hthant/snowteam_2023_2024/CFD/DPM/DPM 5/DPM Attempt 5_files/dp0/FFF-1/Fluent/animation-1_0196.png

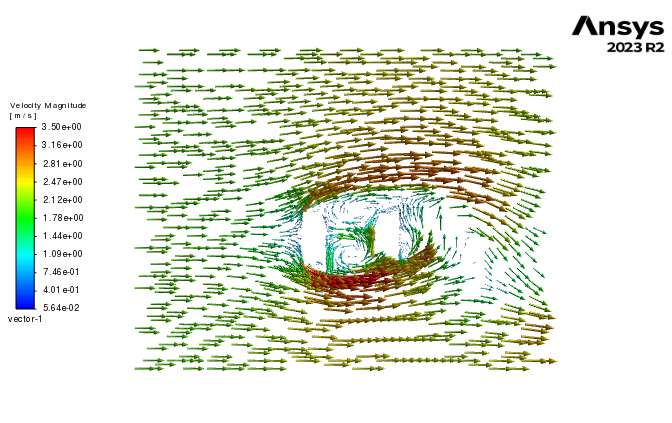
CFD/DPM/DPM 5/DPM Attempt 5_files/dp0/FFF-1/Fluent/animation-1_0196.png
