hthant/snowteam_2023_2024/CFD/Different Diameters/7_5_inch_diameter_files/progress_files/dp0/FFF-1/Fluent/vector-1.png

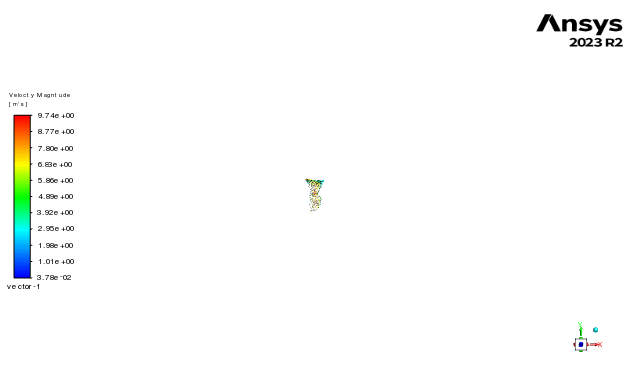
CFD/Different Diameters/7_5_inch_diameter_files/progress_files/dp0/FFF-1/Fluent/vector-1.png
