hthant/snowteam_2023_2024/CFD/DPM/DPM 5/Capture4.PNG

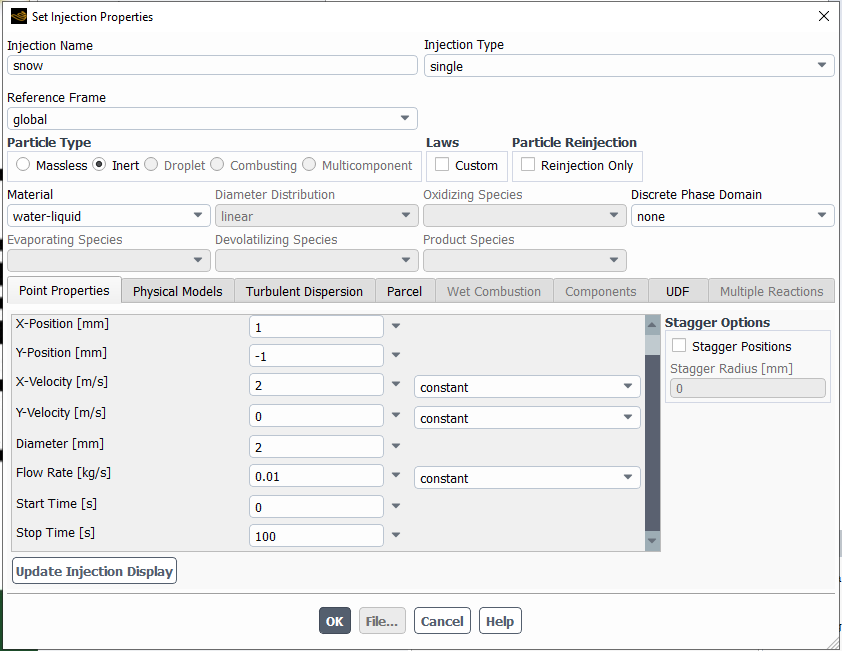
CFD/DPM/DPM 5/Capture4.PNG
