hthant/snowteam_2023_2024/CFD/DPM/DPM_Attempt1_files/progress_files/dp0/FFF/Fluent/particle-tracks-1.png

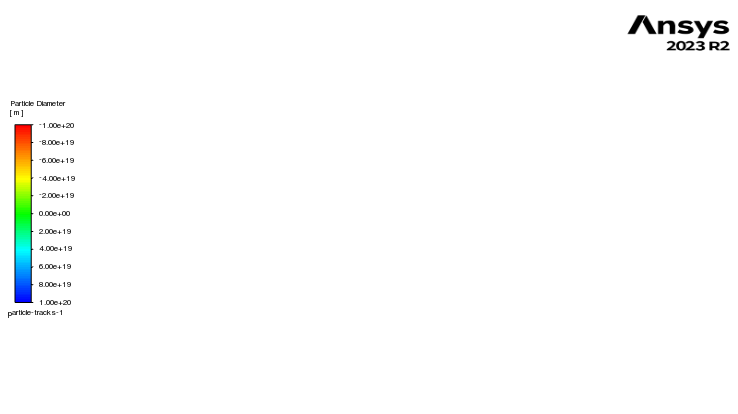
CFD/DPM/DPM_Attempt1_files/progress_files/dp0/FFF/Fluent/particle-tracks-1.png
