hthant/snowteam_2023_2024/Light Fixtures/Heatsink/Heatsink model with holes.png

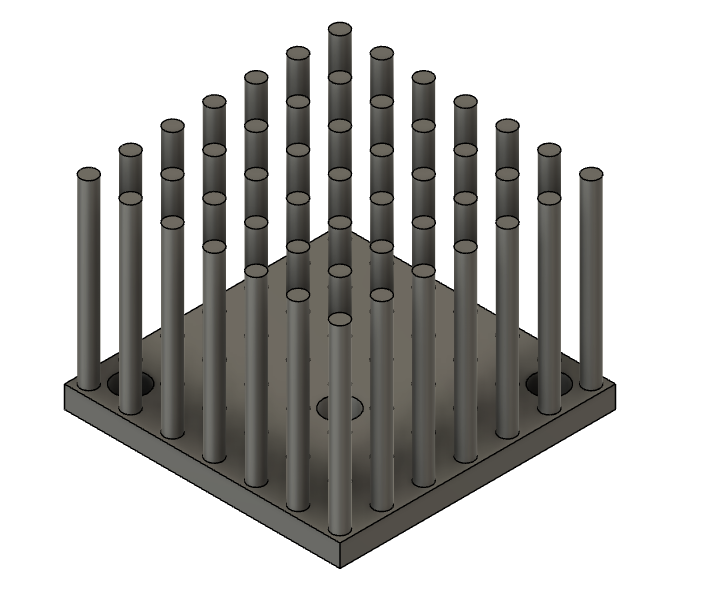
Light Fixtures/Heatsink/Heatsink model with holes.png
