hthant/snowteam_2023_2024/Light Fixtures/Heatsink/HoleDiagram.png

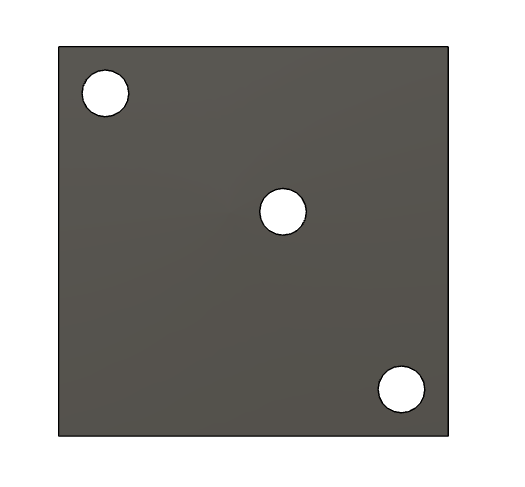
Light Fixtures/Heatsink/HoleDiagram.png
