hthant/snowteam_2023_2024/Light Fixtures/Heatsink/HoleDimensions.png

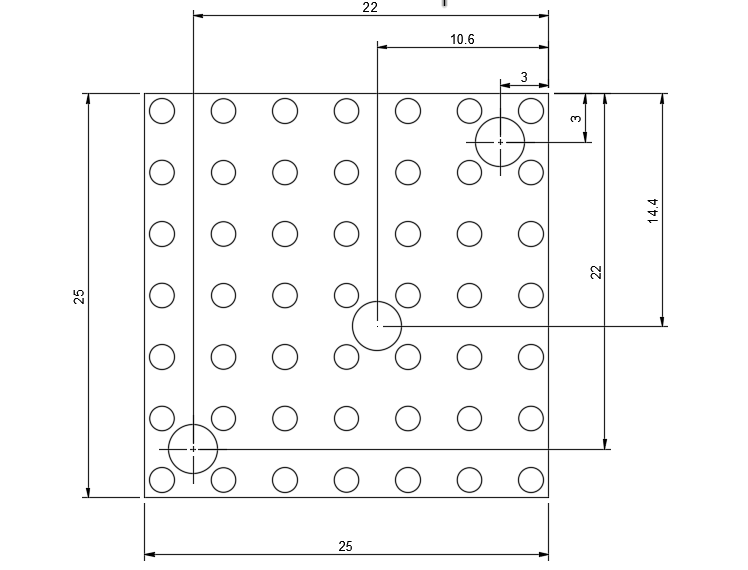
Light Fixtures/Heatsink/HoleDimensions.png
