hthant/snowteam_2023_2024/MASC photos/IMG-0106.jpg

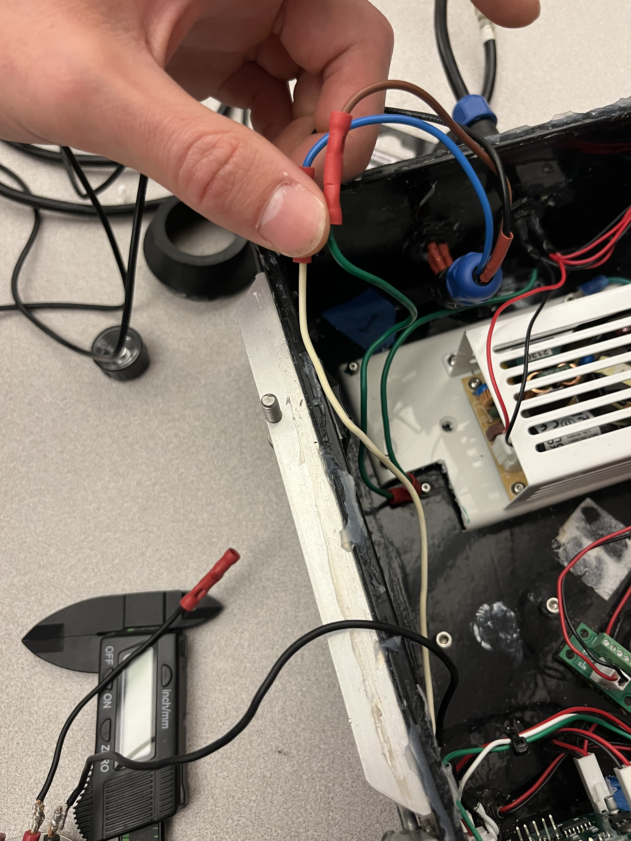
MASC photos/IMG-0106.jpg
