hthant/snowteam_2023_2024/Spot Size Part/stick2mmdiam.SLDPRT

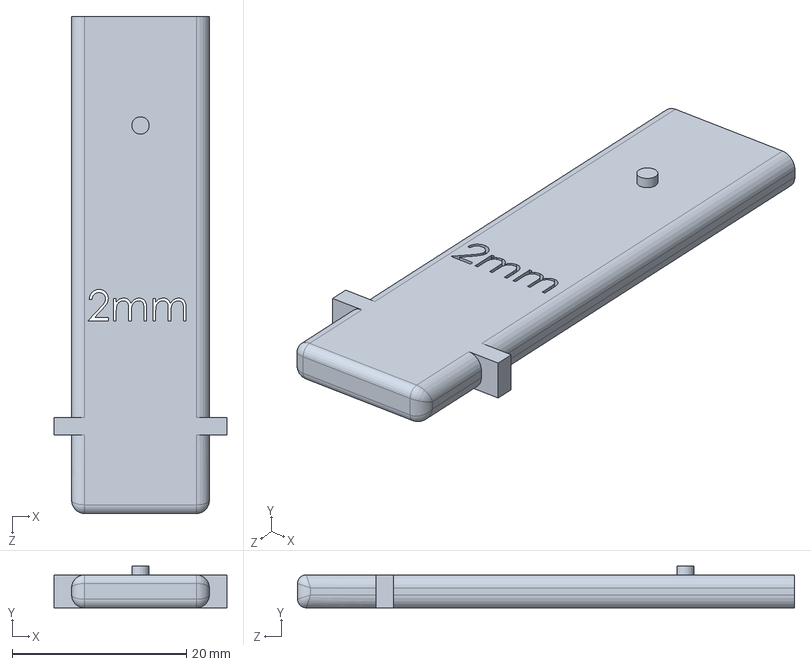
[picture p60: CAD file, 2024-04-29]
Spot Size Part/stick2mmdiam.SLDPRT
19.8 x 4.80 x 57.0 mm
