hthant/snowteam_2023_2024/CFD/Conical SMAS Designs/Solidworks/Test_Print_Conical_Base.SLDPRT

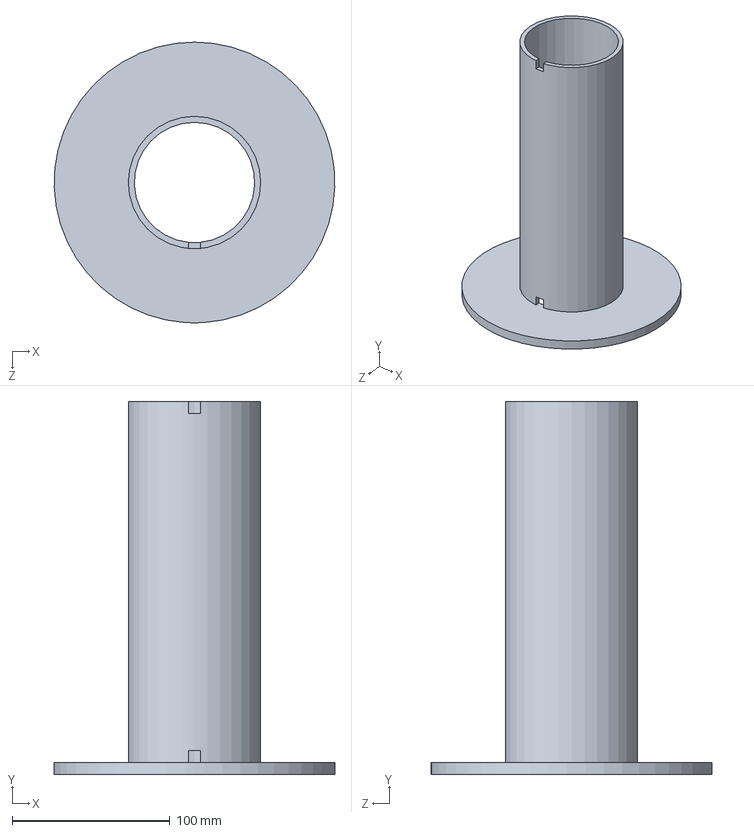
[picture p61: CAD file, 2024-05-03]
CFD/Conical SMAS Designs/Solidworks/Test_Print_Conical_Base.SLDPRT
177.7 x 236.2 x 177.8 mm
