hthant/snowteam_2023_2024/LED Pen/HexPenBasic.SLDPRT

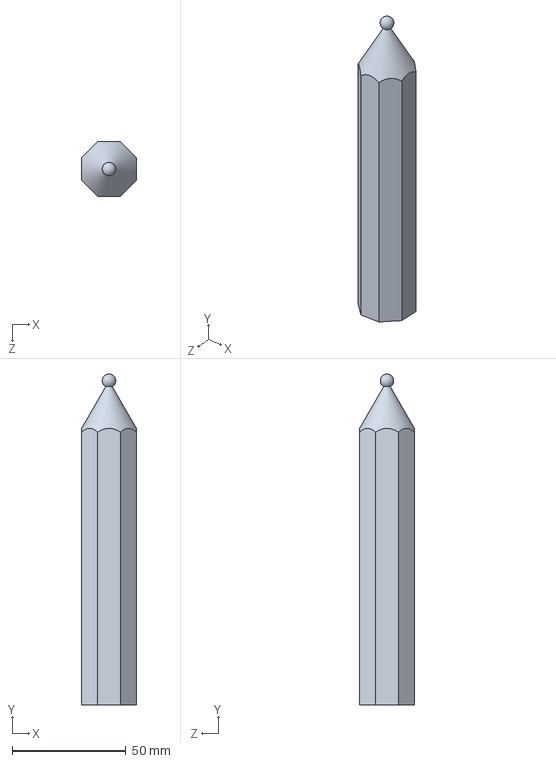
[picture p62: CAD file, 2024-04-29]
LED Pen/HexPenBasic.SLDPRT
24.1 x 145.6 x 24.1 mm
