hthant/snowteam_2023_2024/Light Fixtures/LED Bracket CAD Files/Horizontal LED Bracket v1.step

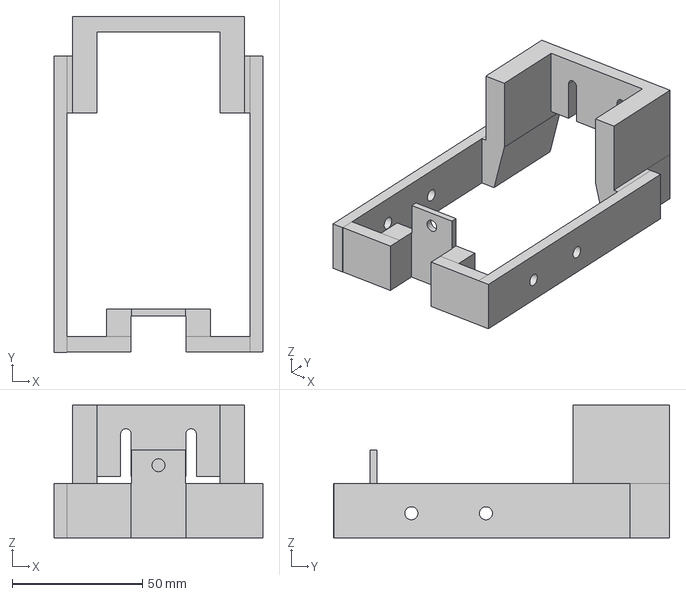
[picture p63: CAD file, 2023-11-14]
Light Fixtures/LED Bracket CAD Files/Horizontal LED Bracket v1.step
80.0 x 128.8 x 50.8 mm
