hthant/snowteam_2023_2024/MASC/3D drawings/CornerPowerSupplyVfinal v0.stl

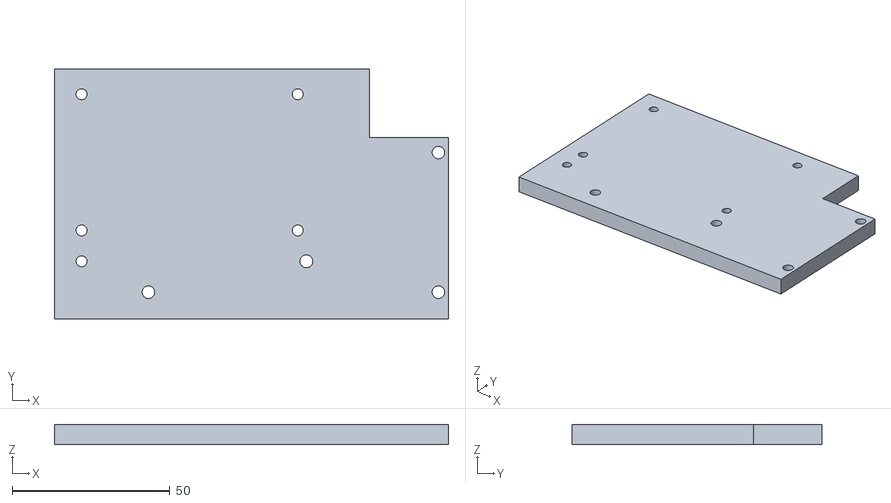
[picture p64: CAD file, 2023-11-14]
MASC/3D drawings/CornerPowerSupplyVfinal v0.stl
125.0 x 79.3 x 6.40
