hthant/snowteam_2023_2024/Resin Printing/Snowflakes/3D_Files/MR,15,2.stl

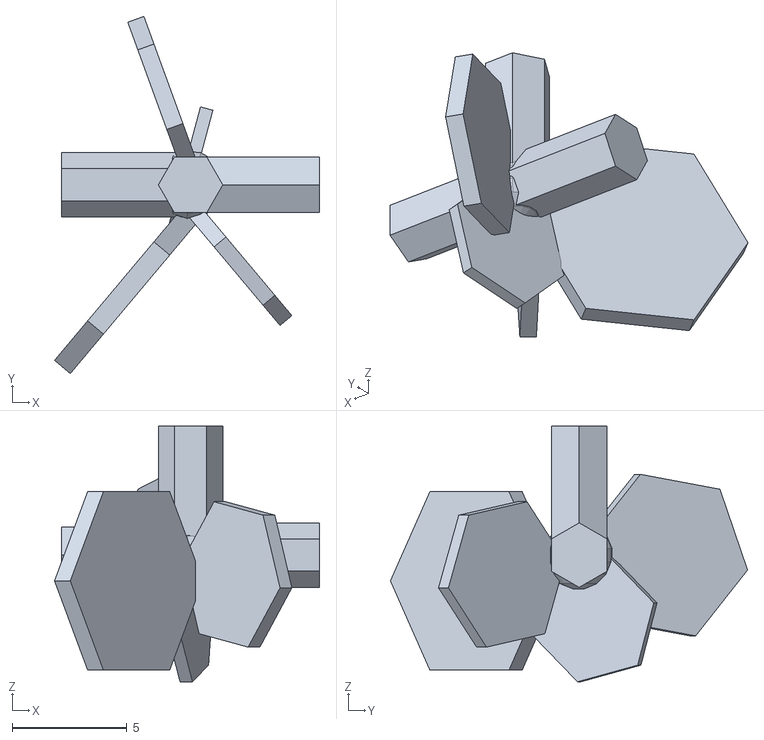
[picture p65: CAD file, 2023-11-13]
Resin Printing/Snowflakes/3D_Files/MR,15,2.stl
11.6 x 15.6 x 11.2
