hthant/snowteam_2023_2024/solidworks_senior_design/test_4nut_quarterinch.SLDPRT

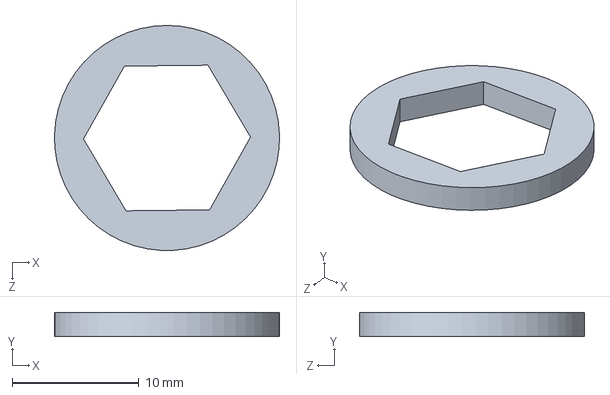
[picture p66: CAD file, 2024-04-25]
solidworks_senior_design/test_4nut_quarterinch.SLDPRT
17.8 x 1.90 x 17.8 mm
