hthant/snowteam_2023_2024/CFD/Models for CFD/VerticalMeshAttempt.SLDPRT

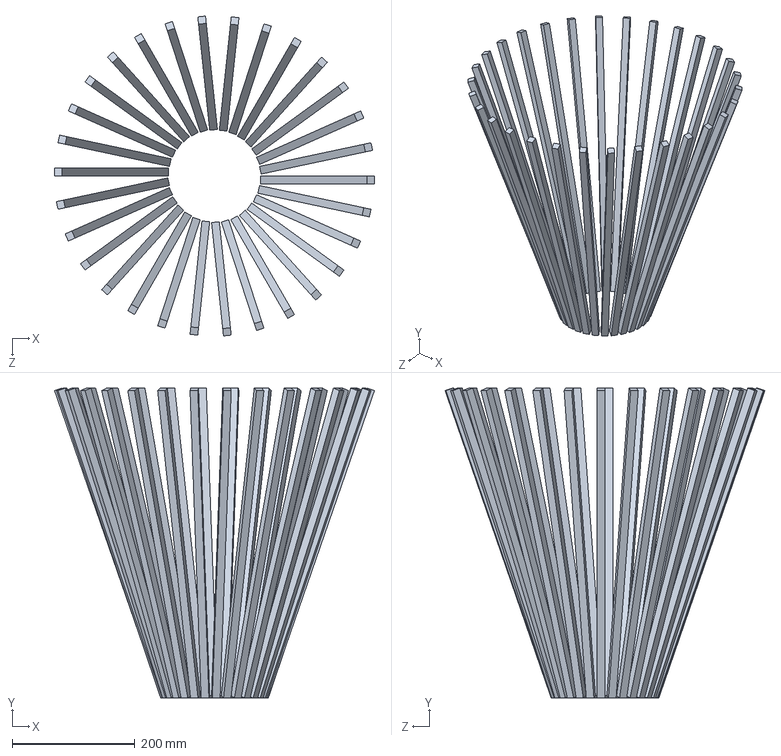
[picture p67: CAD file, 2024-05-03]
CFD/Models for CFD/VerticalMeshAttempt.SLDPRT
521.0 x 504.5 x 520.8 mm
