hthant/snowteam_2023_2024/Desiccant Box/DesiccantBox.SLDPRT

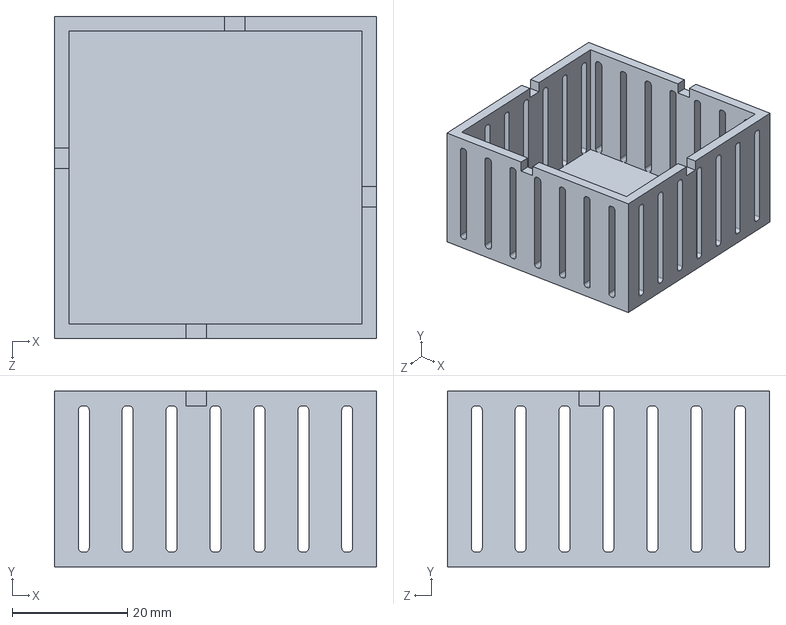
[picture p68: CAD file, 2024-04-29]
Desiccant Box/DesiccantBox.SLDPRT
55.9 x 30.5 x 55.9 mm
