hthant/snowteam_2023_2024/LED Pen/CircuitBoard.SLDPRT

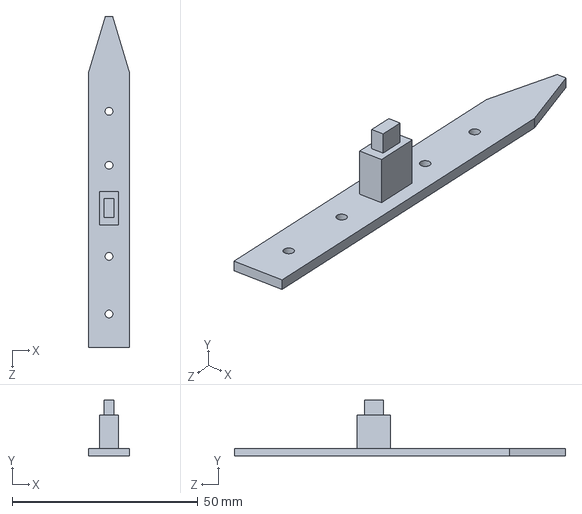
[picture p69: CAD file, 2023-11-12]
LED Pen/CircuitBoard.SLDPRT
11.0 x 15.0 x 89.0 mm
