hthant/snowteam_2023_2024/Light Fixtures/LED Bracket CAD Files/Horizontal LED Bracket no laser v1.step

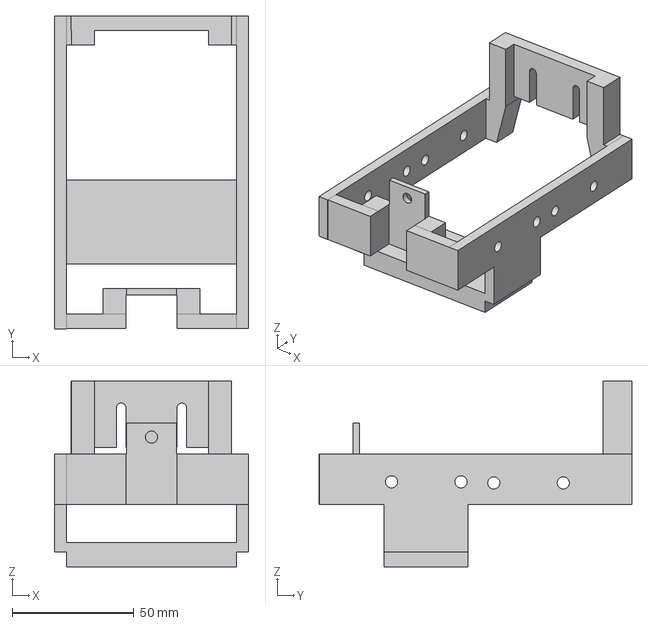
[picture p70: CAD file, 2023-11-14]
Light Fixtures/LED Bracket CAD Files/Horizontal LED Bracket no laser v1.step
80.0 x 128.8 x 76.3 mm
