hthant/snowteam_2023_2024/Resin Printing/Snowflakes/3D_Files/Ag,1,St18.stl

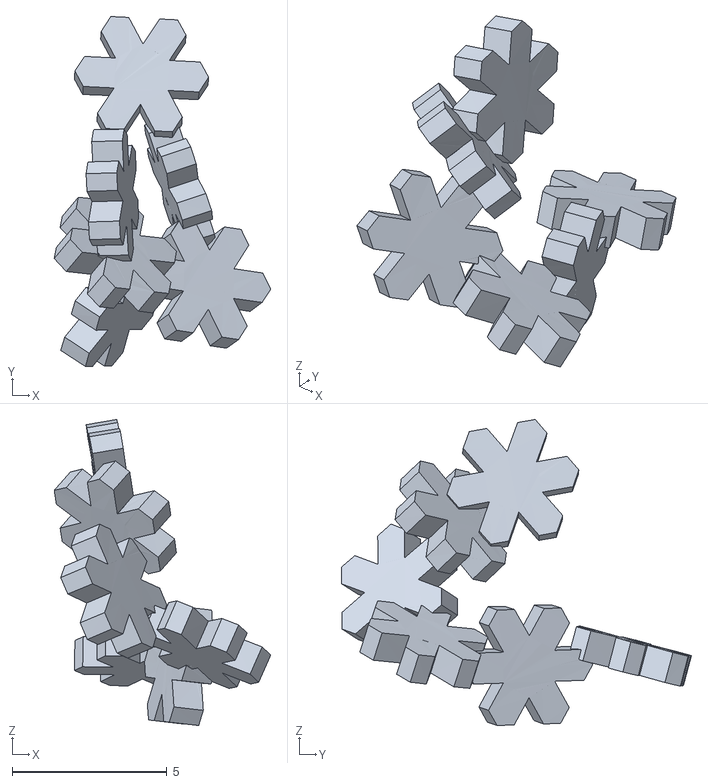
[picture p71: CAD file, 2023-11-13]
Resin Printing/Snowflakes/3D_Files/Ag,1,St18.stl
7.00 x 11.3 x 9.89
