hthant/snowteam_2023_2024/solidworks_senior_design/alignment_tip.SLDPRT

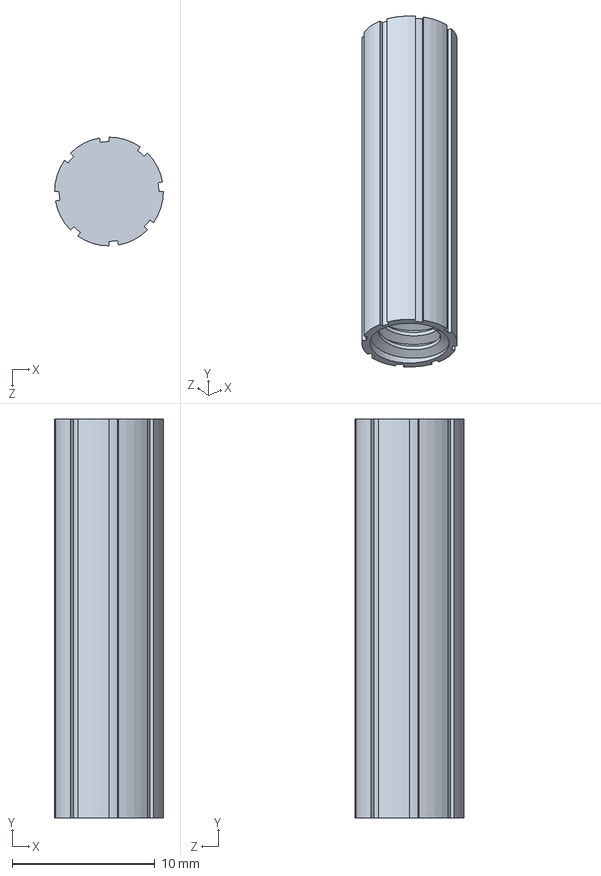
[picture p72: CAD file, 2024-04-25]
solidworks_senior_design/alignment_tip.SLDPRT
7.62 x 27.9 x 7.62 mm
