hthant/snowteam_2023_2024/LED Pen/PenAgain.SLDPRT

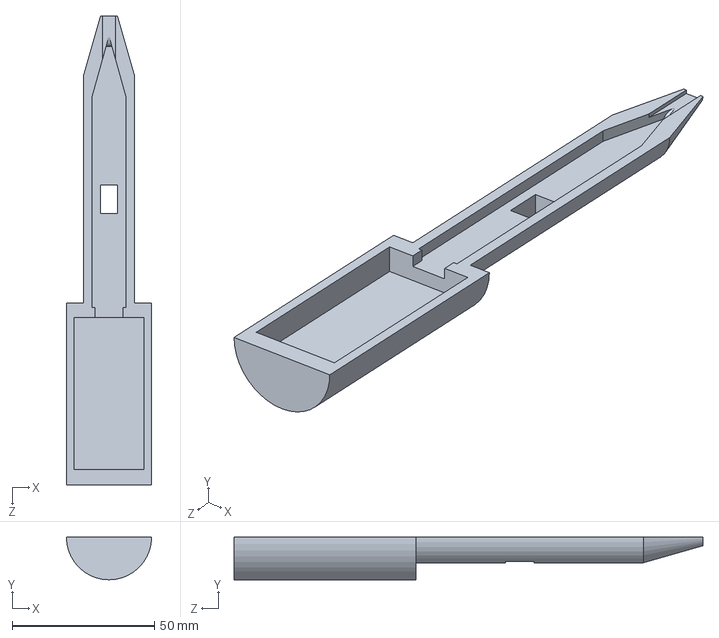
[picture p73: CAD file, 2023-11-12]
LED Pen/PenAgain.SLDPRT
30.0 x 15.0 x 165.0 mm
