hthant/snowteam_2023_2024/Light Fixtures/LED Bracket CAD Files/LEDHolder v1.step

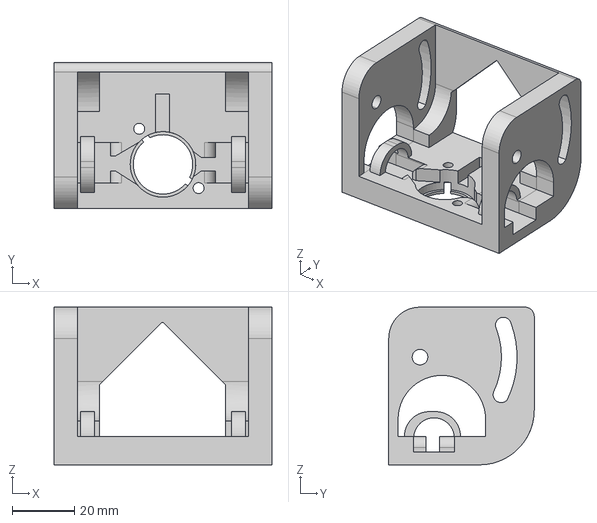
[picture p74: CAD file, 2023-11-14]
Light Fixtures/LED Bracket CAD Files/LEDHolder v1.step
69.8 x 46.6 x 50.5 mm
