hthant/snowteam_2023_2024/Resin Printing/Snowflakes/3D_Files/MR,10,1.stl

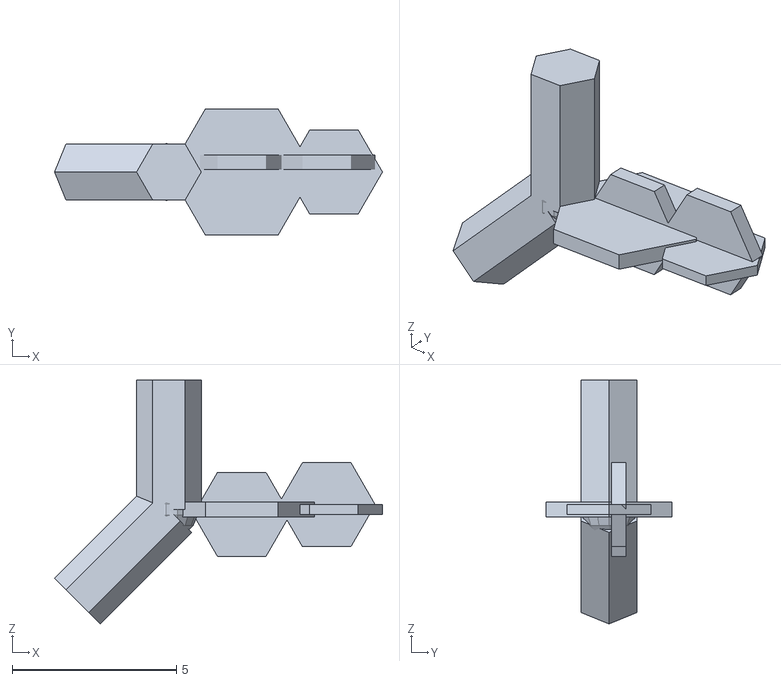
[picture p75: CAD file, 2023-11-13]
Resin Printing/Snowflakes/3D_Files/MR,10,1.stl
10.00 x 3.85 x 7.44
