hthant/snowteam_2023_2024/solidworks_senior_design/lightblockerbottomsecondhalf2.SLDPRT

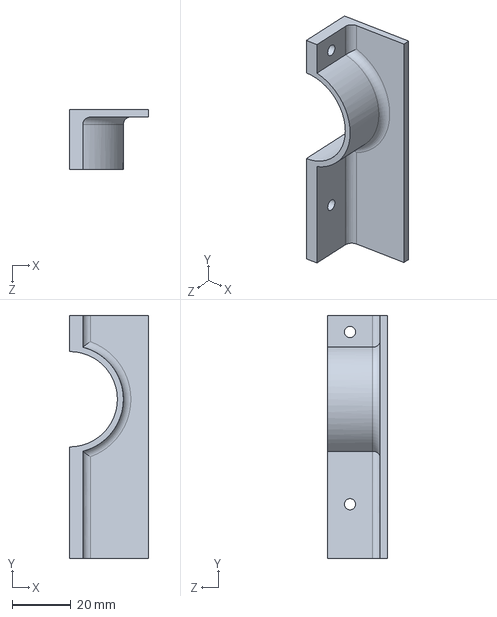
[picture p76: CAD file, 2023-11-08]
solidworks_senior_design/lightblockerbottomsecondhalf2.SLDPRT
26.7 x 82.5 x 20.3 mm
