hthant/snowteam_2023_2024/CFD/Conical SMAS Designs/Solidworks/Test_Print_Conical_Cap.SLDPRT

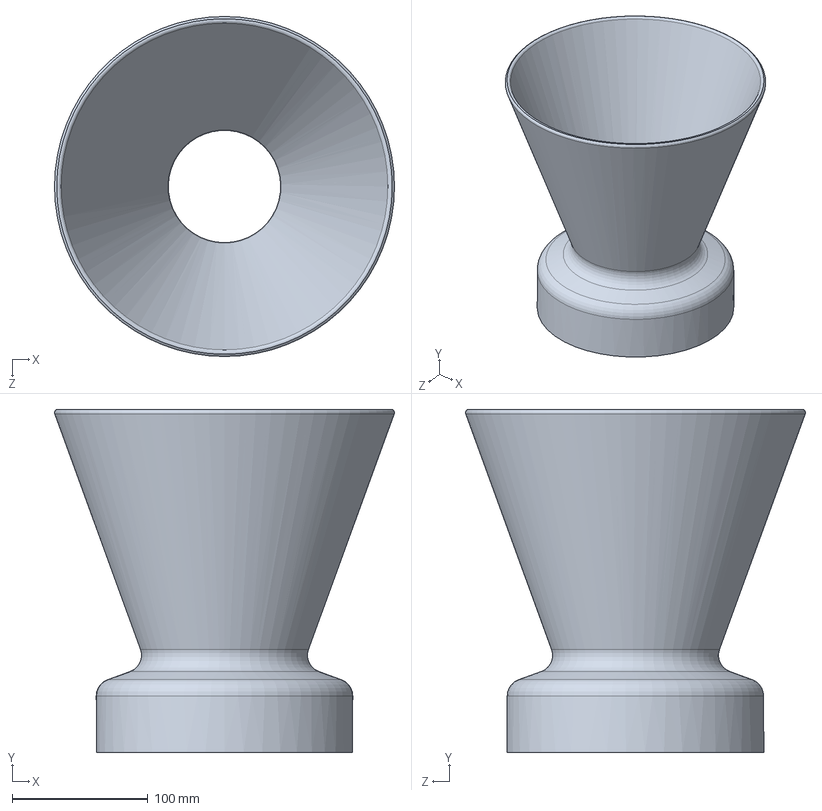
[picture p77: CAD file, 2024-05-03]
CFD/Conical SMAS Designs/Solidworks/Test_Print_Conical_Cap.SLDPRT
250.7 x 253.3 x 250.7 mm
