hthant/snowteam_2023_2024/CFD/Models for CFD/Conical_20_degree_With_Bottom_Cone.STEP

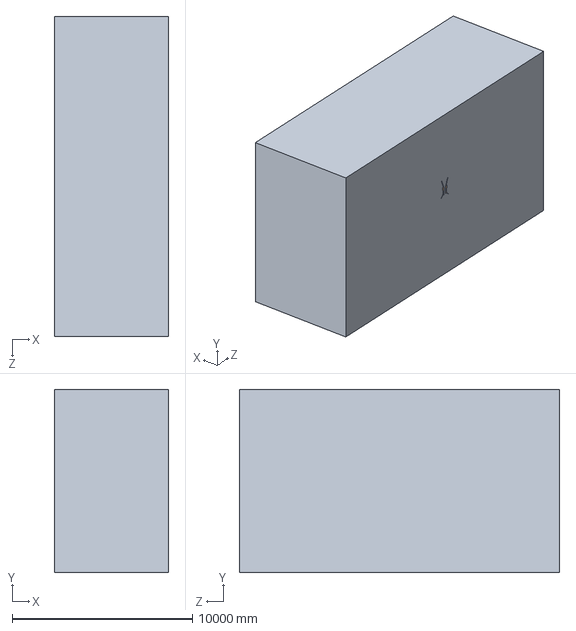
[picture p78: CAD file, 2024-05-03]
CFD/Models for CFD/Conical_20_degree_With_Bottom_Cone.STEP
6350.0 x 10160.0 x 17780.0 mm
