hthant/snowteam_2023_2024/LED Pen/PenAgainSide2.SLDPRT

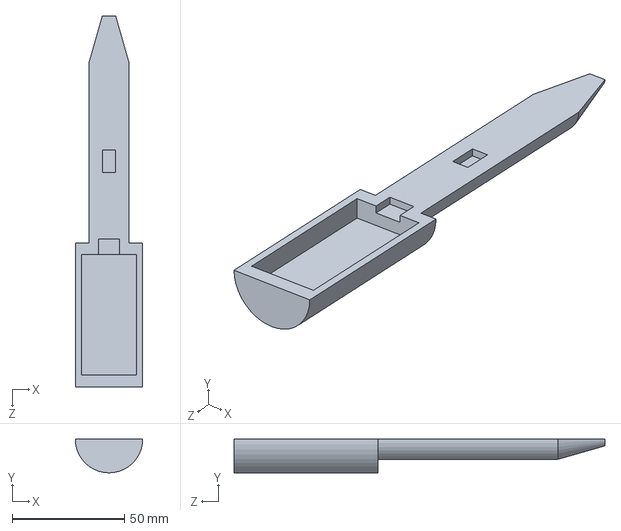
[picture p79: CAD file, 2023-11-12]
LED Pen/PenAgainSide2.SLDPRT
30.0 x 15.0 x 165.0 mm
