hthant/snowteam_2023_2024/Resin Printing/Snowflakes/3D_Files/Ag,4,Cr77_fixed.stl

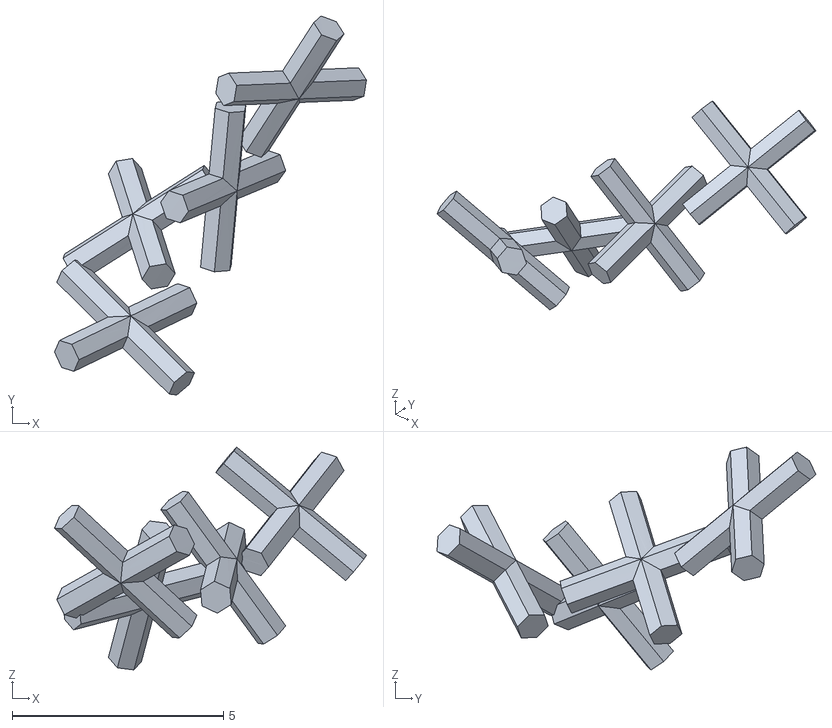
[picture p80: CAD file, 2023-11-13]
Resin Printing/Snowflakes/3D_Files/Ag,4,Cr77_fixed.stl
7.39 x 8.97 x 5.28
