hthant/snowteam_2023_2024/Resin Printing/Snowflakes/3D_Files/Ag,1.5,St100.stl

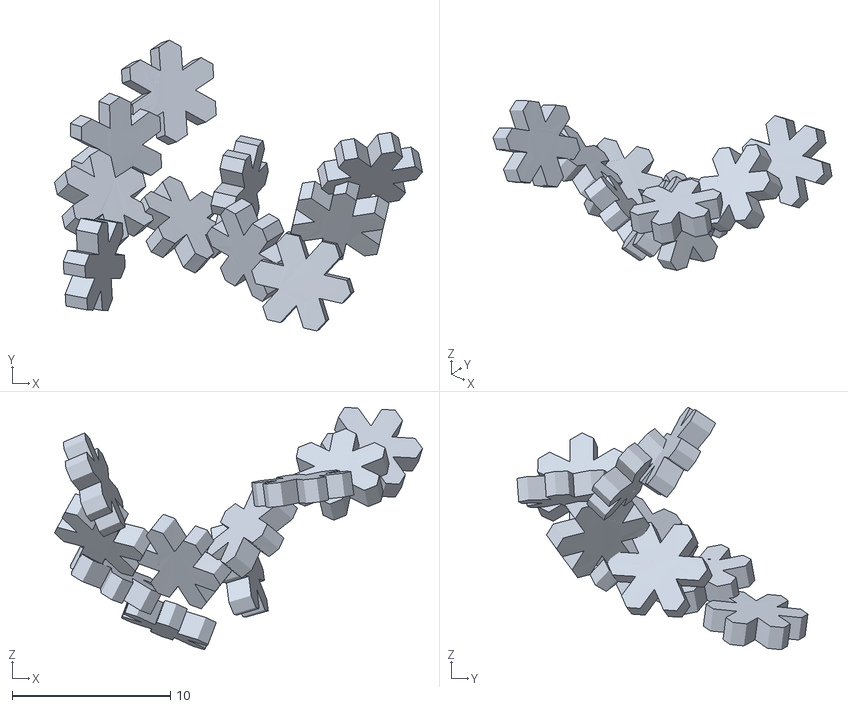
[picture p81: CAD file, 2023-11-13]
Resin Printing/Snowflakes/3D_Files/Ag,1.5,St100.stl
23.3 x 18.4 x 15.3
