hthant/snowteam_2023_2024/solidworks_senior_design/lightblockerbottomhalf2.SLDPRT

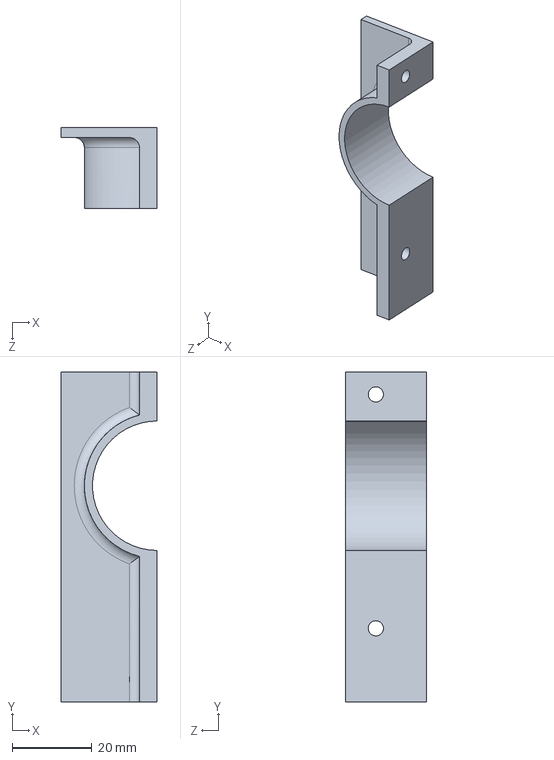
[picture p82: CAD file, 2023-11-08]
solidworks_senior_design/lightblockerbottomhalf2.SLDPRT
24.1 x 82.5 x 20.3 mm
