hthant/snowteam_2023_2024/CFD/Models for CFD/PyramidInCircleWithSolidCylinder.SLDPRT

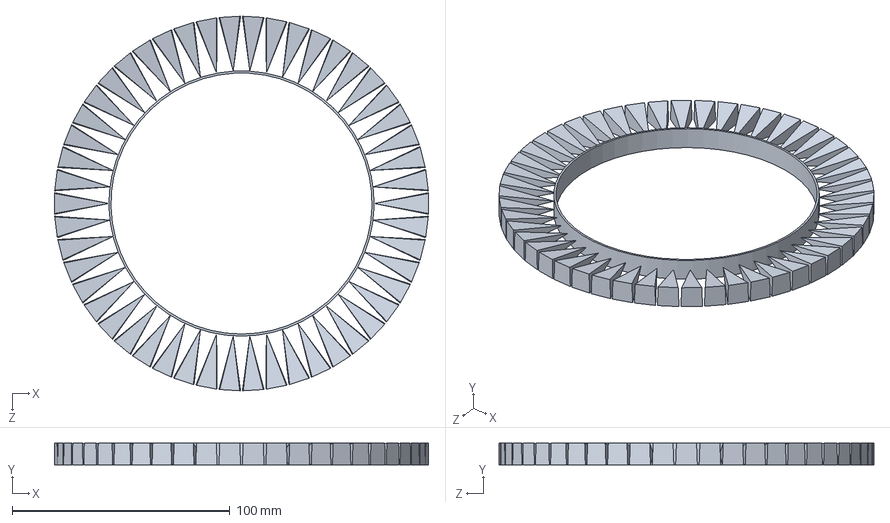
[picture p83: CAD file, 2024-05-03]
CFD/Models for CFD/PyramidInCircleWithSolidCylinder.SLDPRT
171.9 x 10.0 x 172.2 mm
