hthant/snowteam_2023_2024/LED Pen/BatteryPack.SLDPRT

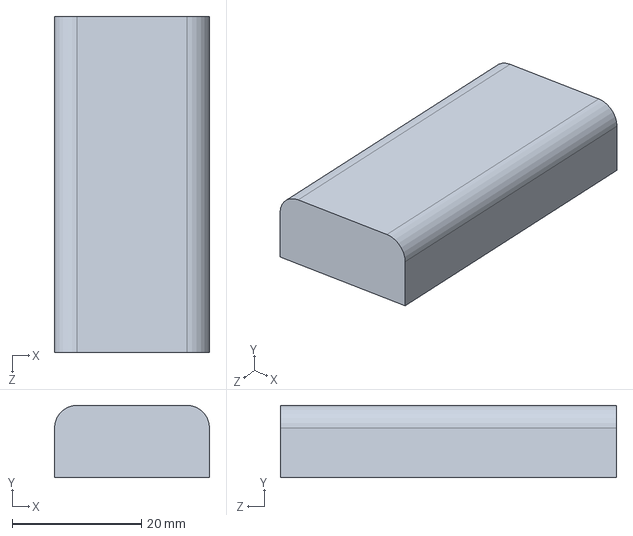
[picture p84: CAD file, 2023-11-12]
LED Pen/BatteryPack.SLDPRT
24.0 x 11.2 x 52.0 mm
