hthant/snowteam_2023_2024/Resin Printing/Snowflakes/3D_Files/Ag,1.25,St100.stl

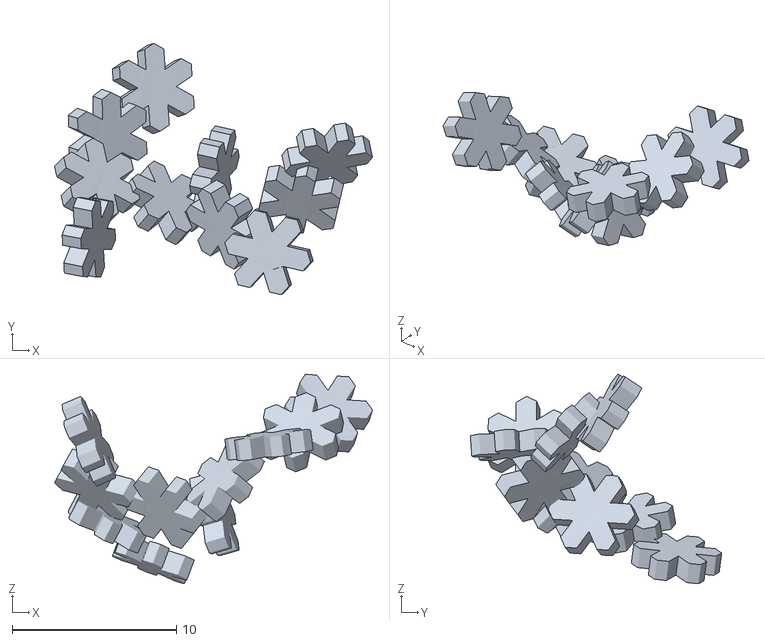
[picture p85: CAD file, 2023-11-13]
Resin Printing/Snowflakes/3D_Files/Ag,1.25,St100.stl
19.4 x 15.3 x 12.8
