hthant/snowteam_2023_2024/solidworks_senior_design/lightblockerhalf2.SLDPRT

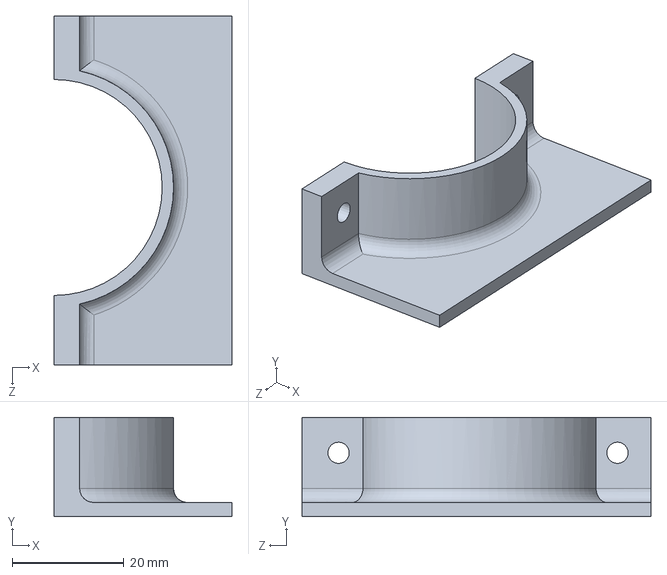
[picture p86: CAD file, 2023-11-08]
solidworks_senior_design/lightblockerhalf2.SLDPRT
31.8 x 17.8 x 62.4 mm
