hthant/snowteam_2023_2024/CFD/Conical SMAS Designs/Solidworks/Test_Print_Conical_Cover.SLDPRT

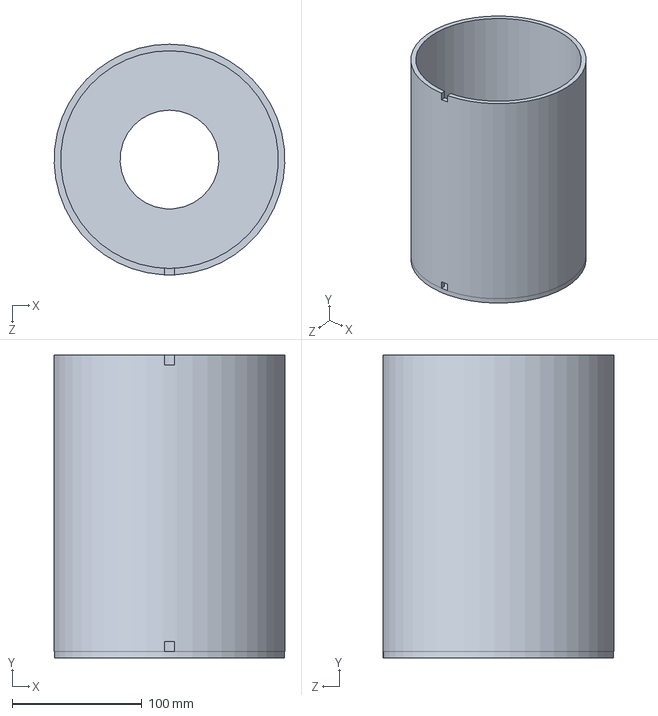
[picture p87: CAD file, 2024-05-03]
CFD/Conical SMAS Designs/Solidworks/Test_Print_Conical_Cover.SLDPRT
177.8 x 233.7 x 177.9 mm
