hthant/snowteam_2023_2024/Resin Printing/Snowflakes/3D_Files/CR,4,5,12.stl

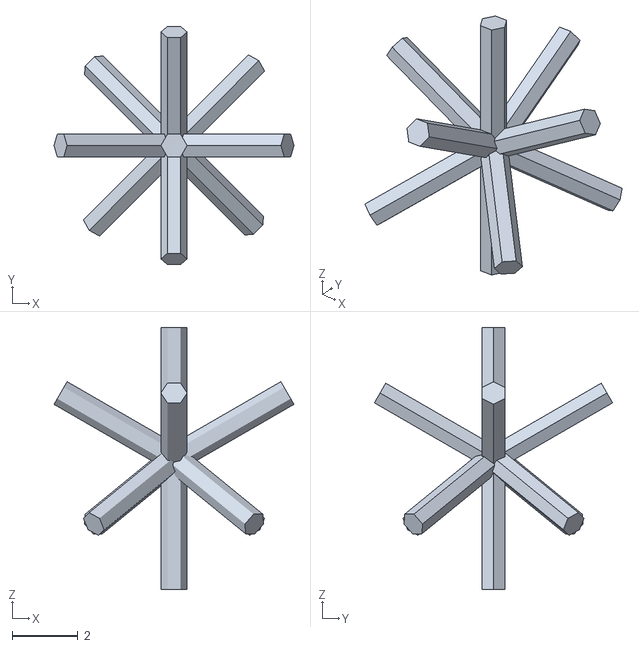
[picture p88: CAD file, 2023-11-13]
Resin Printing/Snowflakes/3D_Files/CR,4,5,12.stl
7.33 x 7.27 x 8.00
