hthant/snowteam_2023_2024/Spot Size Part/stick10mmdiam.SLDPRT

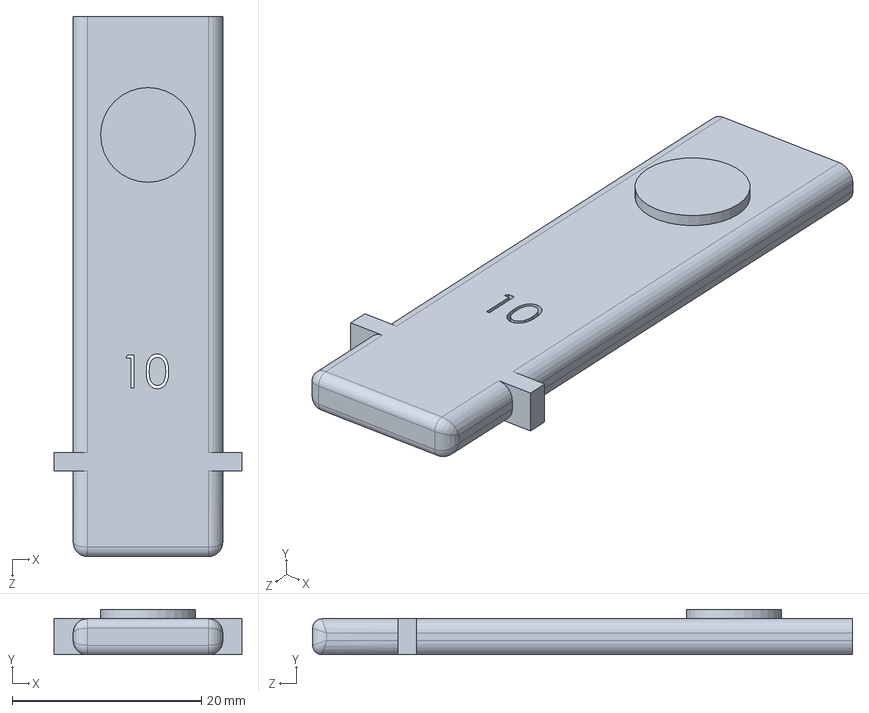
[picture p89: CAD file, 2024-04-29]
Spot Size Part/stick10mmdiam.SLDPRT
19.8 x 4.80 x 57.0 mm
