hthant/snowteam_2023_2024/CFD/Conical SMAS Designs/Solidworks/Possible_CFD_Model.SLDPRT

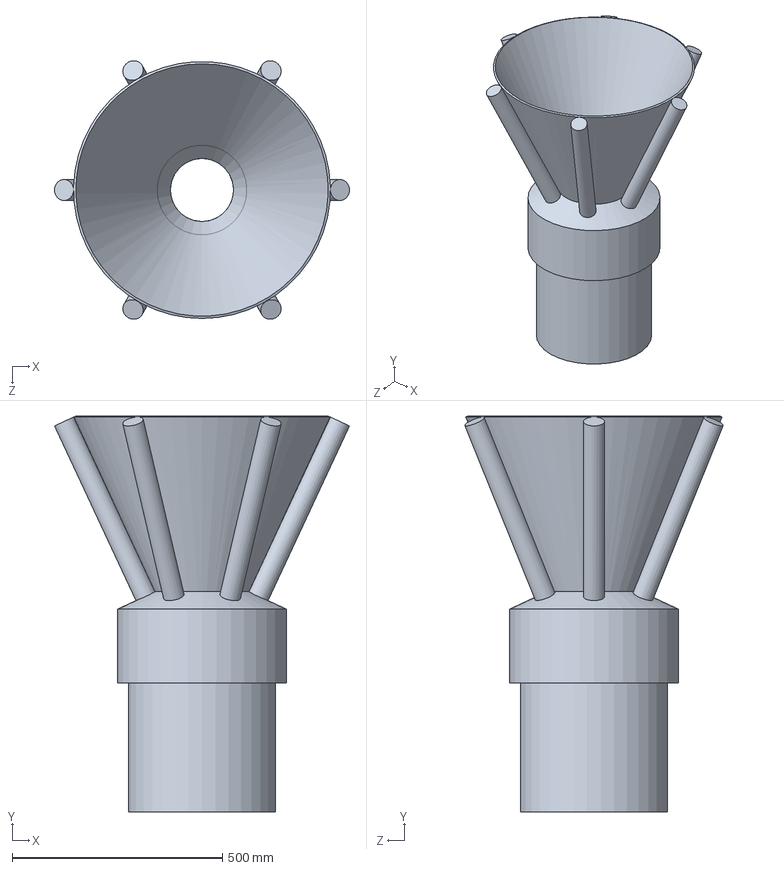
[picture p90: CAD file, 2024-05-03]
CFD/Conical SMAS Designs/Solidworks/Possible_CFD_Model.SLDPRT
701.4 x 941.3 x 614.5 mm
