hthant/snowteam_2023_2024/Spot Size Part/Base.SLDPRT

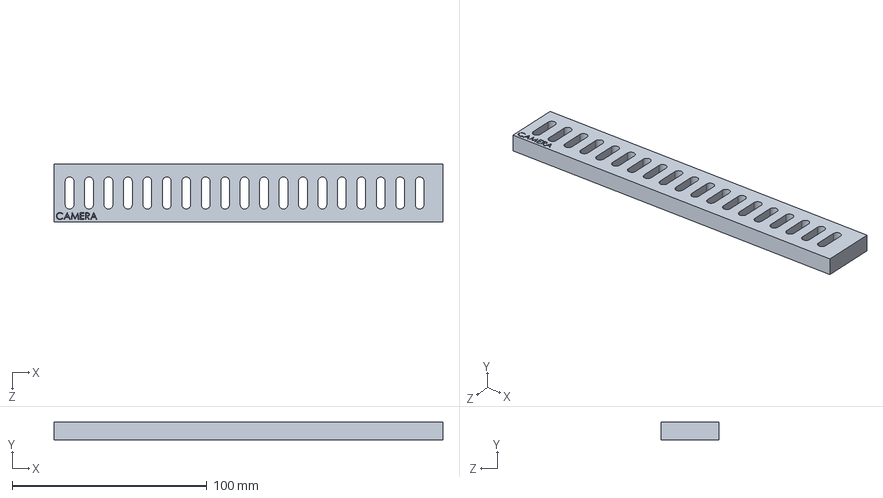
[picture p91: CAD file, 2024-04-29]
Spot Size Part/Base.SLDPRT
200.0 x 9.00 x 30.0 mm
