hthant/snowteam_2023_2024/Resin Printing/Snowflakes/3D_Files/Ag,20,P1.stl

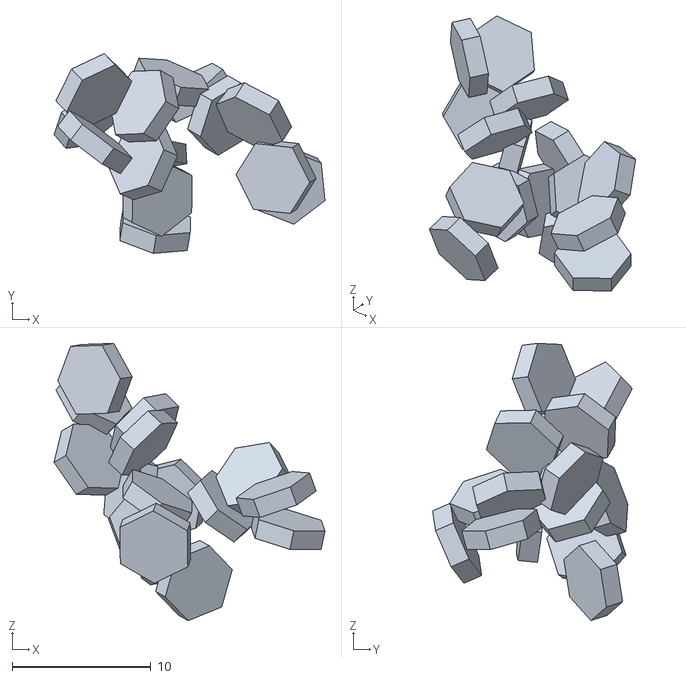
[picture p92: CAD file, 2023-11-13]
Resin Printing/Snowflakes/3D_Files/Ag,20,P1.stl
19.5 x 14.4 x 20.0
