hthant/snowteam_2023_2024/solidworks_senior_design/plexyglass_prototype.SLDPRT

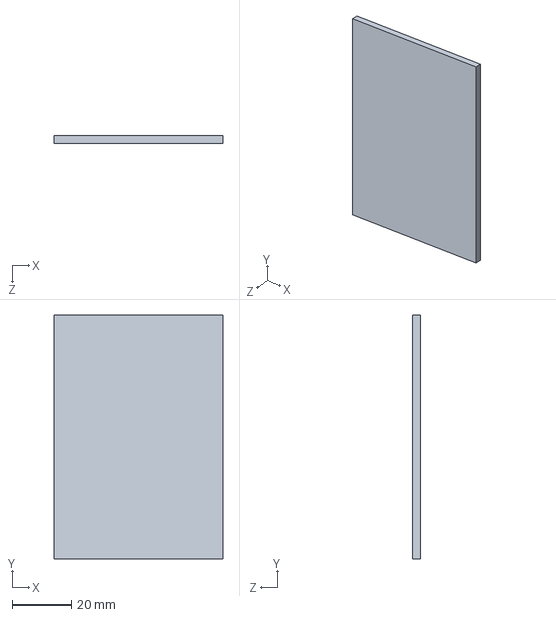
[picture p93: CAD file, 2023-11-08]
solidworks_senior_design/plexyglass_prototype.SLDPRT
56.9 x 82.3 x 2.54 mm
