hthant/snowteam_2023_2024/Resin Printing/Snowflakes/3D_Files/Ag,15,P1.stl

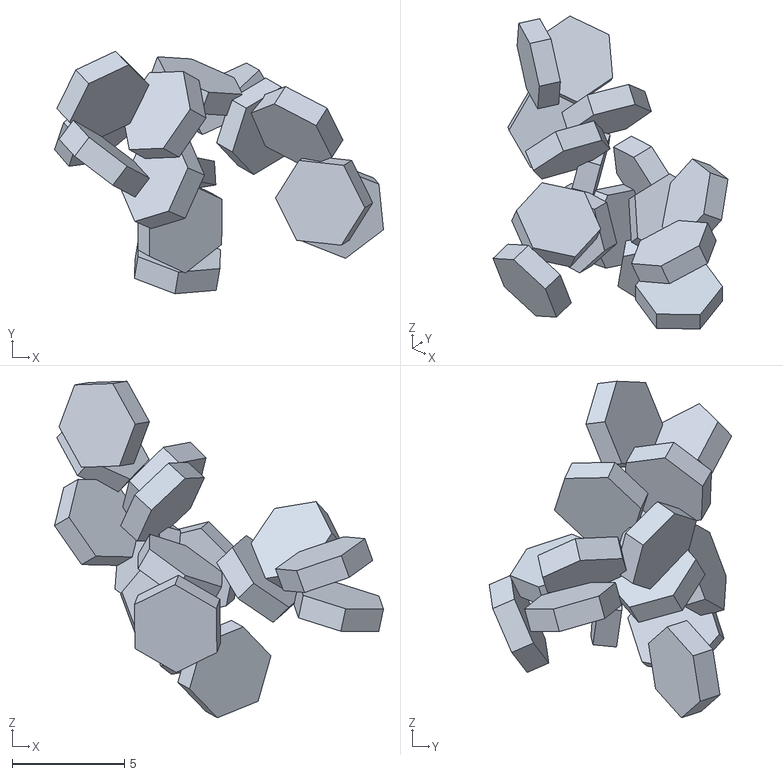
[picture p94: CAD file, 2023-11-13]
Resin Printing/Snowflakes/3D_Files/Ag,15,P1.stl
14.7 x 10.8 x 15.0
