hthant/snowteam_2023_2024/solidworks_senior_design/lightblockerbottomsecondhalf1.SLDPRT

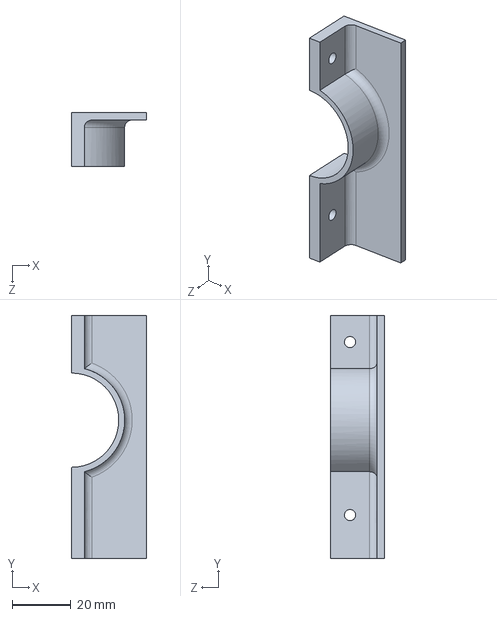
[picture p95: CAD file, 2023-11-08]
solidworks_senior_design/lightblockerbottomsecondhalf1.SLDPRT
25.4 x 82.5 x 18.3 mm
