hthant/snowteam_2023_2024/Resin Printing/Snowflakes/3D_Files/MR,17.5,2.stl

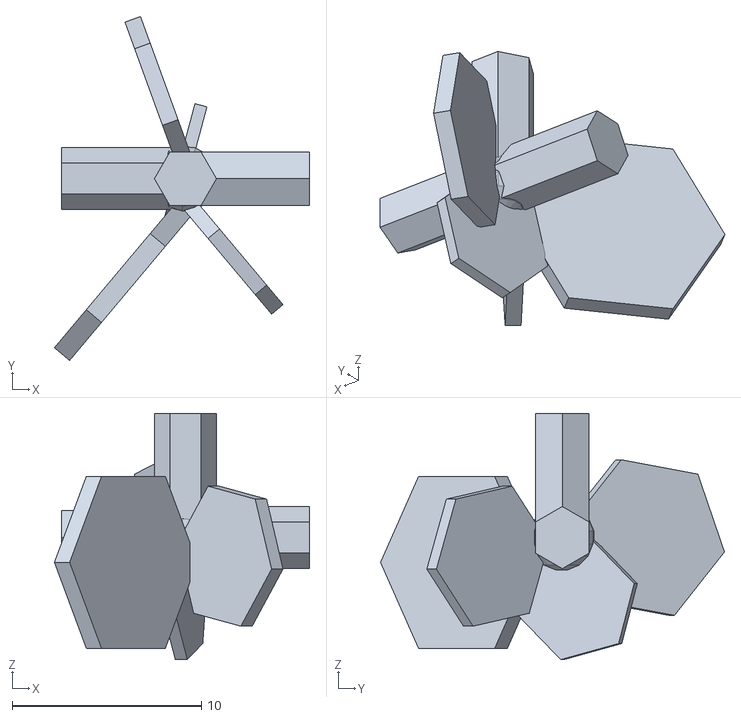
[picture p96: CAD file, 2023-11-13]
Resin Printing/Snowflakes/3D_Files/MR,17.5,2.stl
13.5 x 18.2 x 13.0
