hthant/snowteam_2023_2024/Resin Printing/Snowflakes/3D_Files/Ag,2,St100.stl

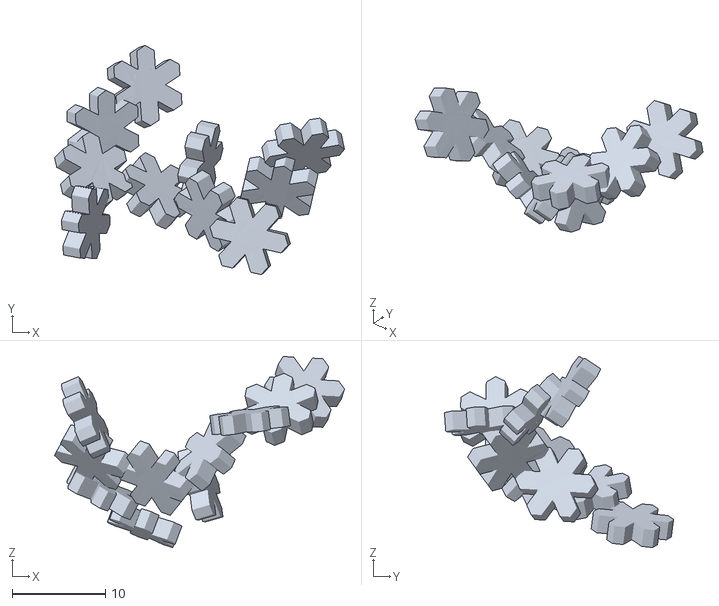
[picture p97: CAD file, 2023-11-13]
Resin Printing/Snowflakes/3D_Files/Ag,2,St100.stl
31.0 x 24.5 x 20.4
