hthant/snowteam_2023_2024/solidworks_senior_design/lightblockerlights.SLDPRT

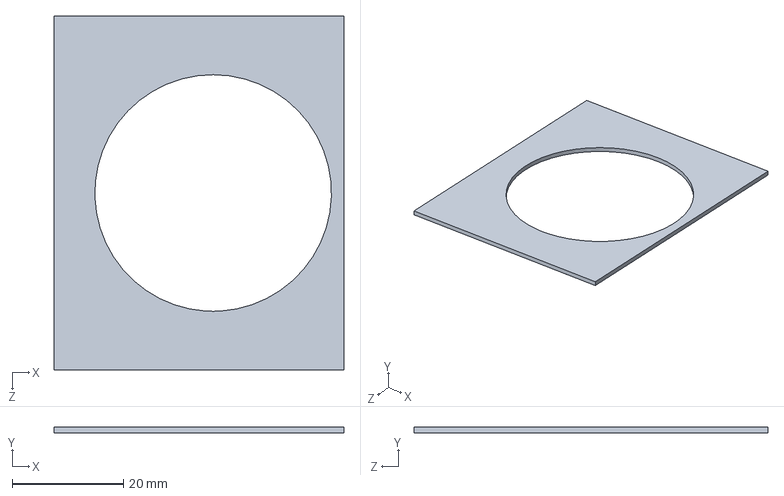
[picture p98: CAD file, 2023-11-08]
solidworks_senior_design/lightblockerlights.SLDPRT
52.1 x 1.00 x 63.5 mm
