hthant/snowteam_2023_2024/Resin Printing/Snowflakes/3D_Files/Ag,8,Cr77_fixed.stl

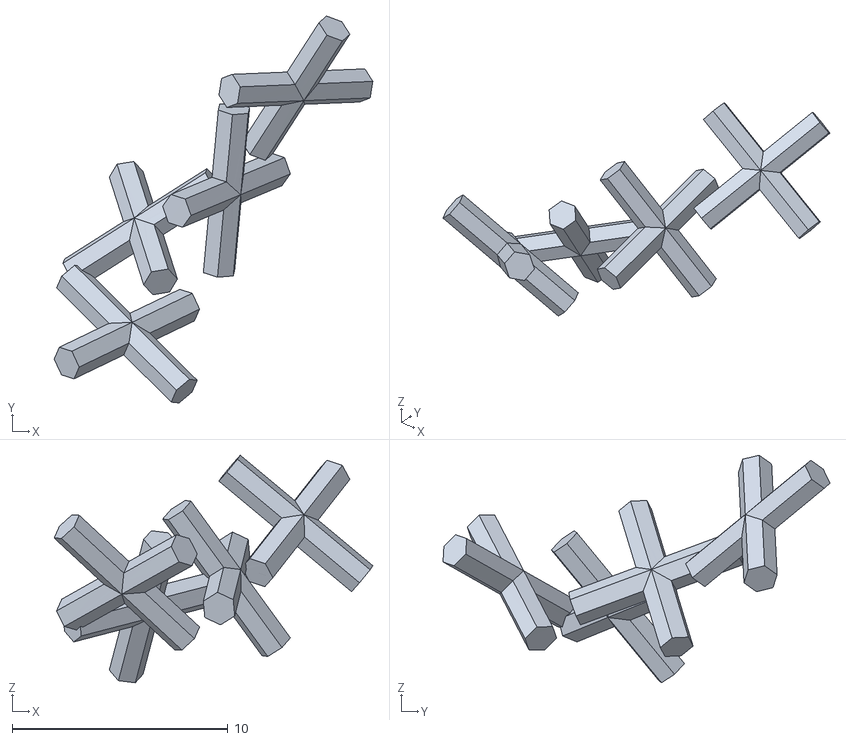
[picture p99: CAD file, 2023-11-13]
Resin Printing/Snowflakes/3D_Files/Ag,8,Cr77_fixed.stl
14.8 x 17.9 x 10.6
