hthant/snowteam_2023_2024/solidworks_senior_design/lightblockerhalf1.SLDPRT

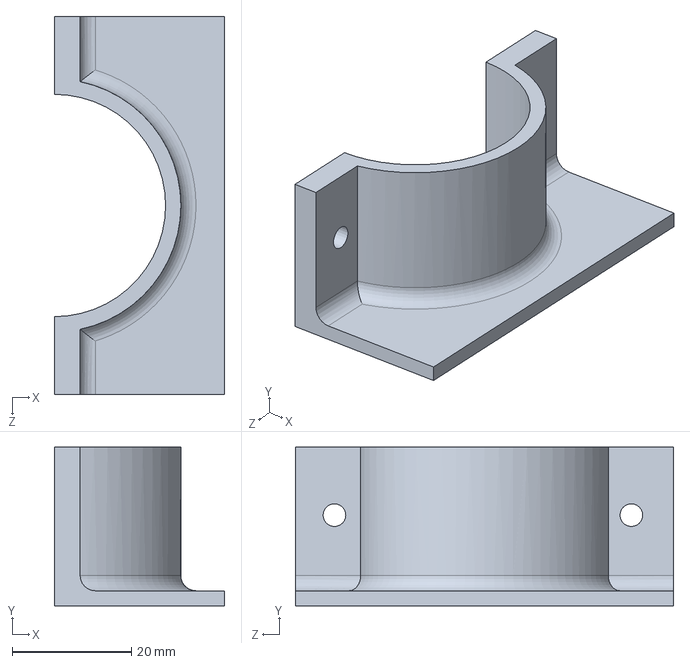
[picture p100: CAD file, 2023-11-08]
solidworks_senior_design/lightblockerhalf1.SLDPRT
28.6 x 26.7 x 63.5 mm
