hthant/snowteam_2023_2024/Resin Printing/Snowflakes/3D_Files/MR,12.5,2.stl

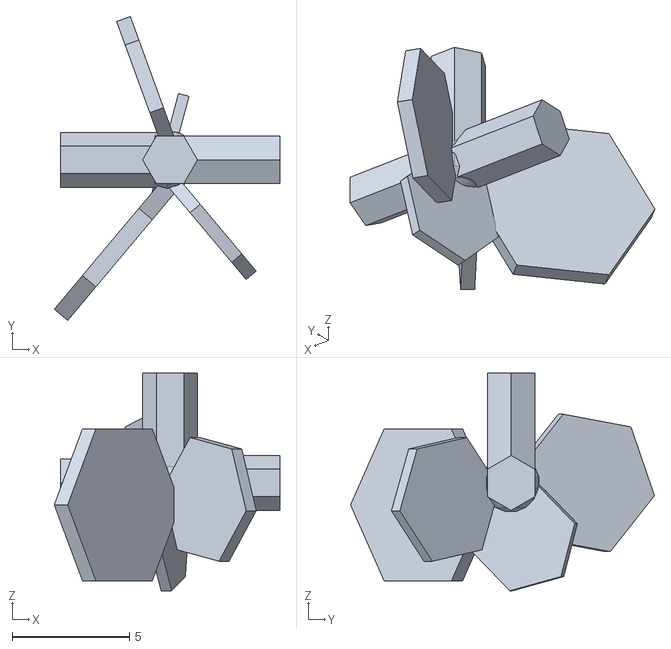
[picture p101: CAD file, 2023-11-13]
Resin Printing/Snowflakes/3D_Files/MR,12.5,2.stl
9.64 x 13.0 x 9.30
