hthant/snowteam_2023_2024/solidworks_senior_design/lightblockerbottomsecondhalf3.SLDPRT

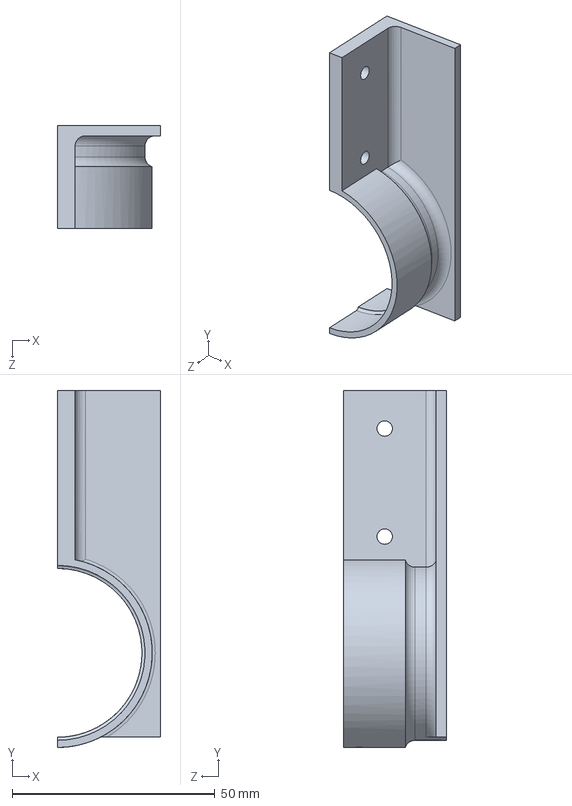
[picture p102: CAD file, 2023-11-08]
solidworks_senior_design/lightblockerbottomsecondhalf3.SLDPRT
25.4 x 88.1 x 25.4 mm
