hthant/snowteam_2023_2024/Resin Printing/Snowflakes/3D_Files/Ag,6,Cr77.stl

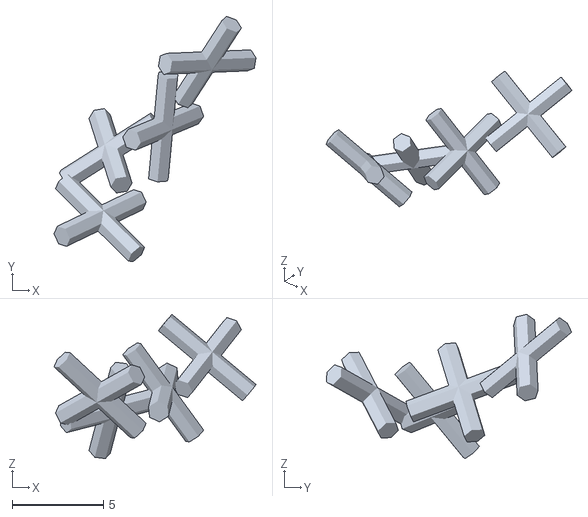
[picture p103: CAD file, 2023-11-13]
Resin Printing/Snowflakes/3D_Files/Ag,6,Cr77.stl
11.1 x 13.5 x 7.92
