hthant/snowteam_2023_2024/Resin Printing/Snowflakes/3D_Files/MR,20,2.stl

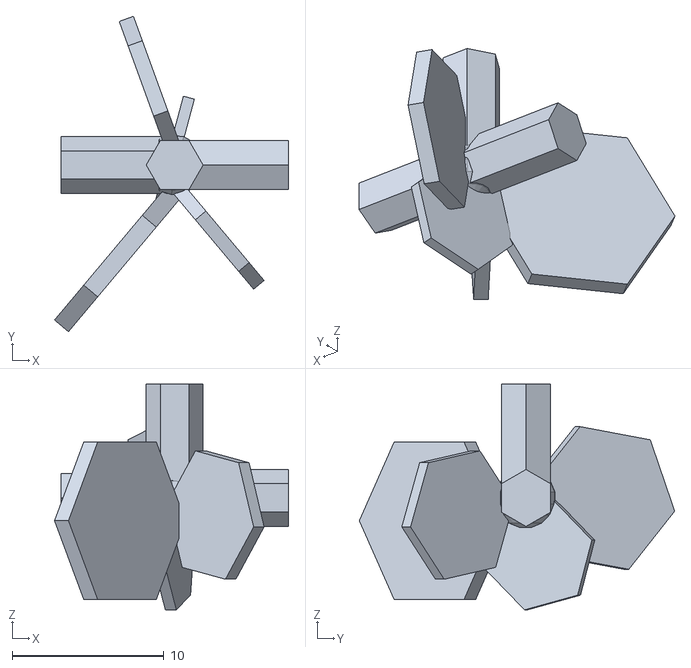
[picture p104: CAD file, 2023-11-13]
Resin Printing/Snowflakes/3D_Files/MR,20,2.stl
15.4 x 20.8 x 14.9
