hthant/snowteam_2023_2024/solidworks_senior_design/lightblockersecondhalf2.SLDPRT

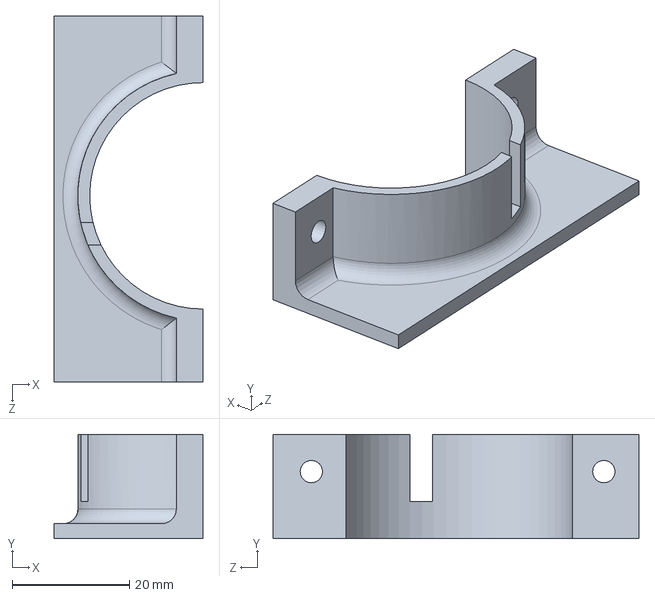
[picture p105: CAD file, 2023-11-08]
solidworks_senior_design/lightblockersecondhalf2.SLDPRT
25.4 x 17.8 x 62.4 mm
