hthant/snowteam_2023_2024/Resin Printing/Snowflakes/3D_Files/Ag,1.5,St18.stl

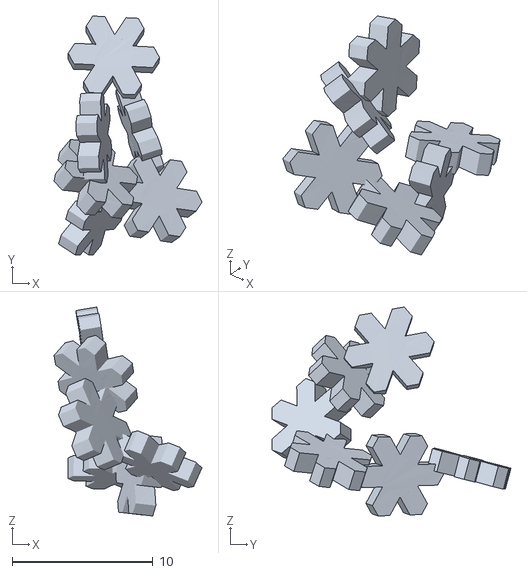
[picture p106: CAD file, 2023-11-13]
Resin Printing/Snowflakes/3D_Files/Ag,1.5,St18.stl
10.5 x 17.0 x 14.8
