hthant/snowteam_2023_2024/Resin Printing/Snowflakes/3D_Files/Ag,1.25,St18.stl

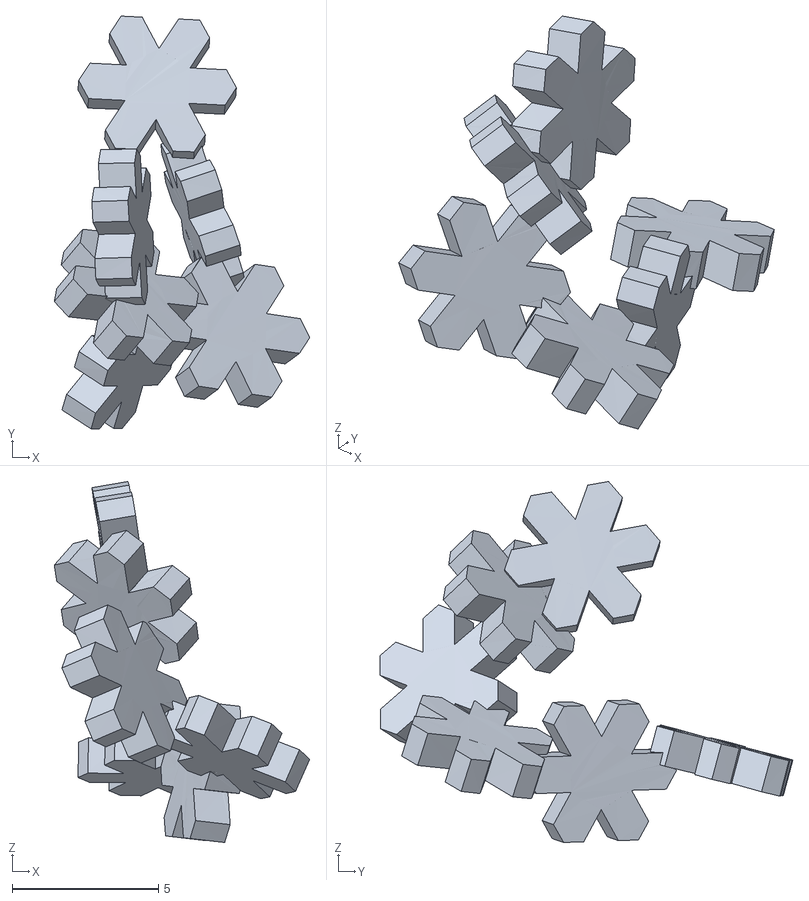
[picture p107: CAD file, 2023-11-13]
Resin Printing/Snowflakes/3D_Files/Ag,1.25,St18.stl
8.75 x 14.1 x 12.4
