hthant/snowteam_2023_2024/Resin Printing/Snowflakes/3D_Files/Ag,1,St100.stl

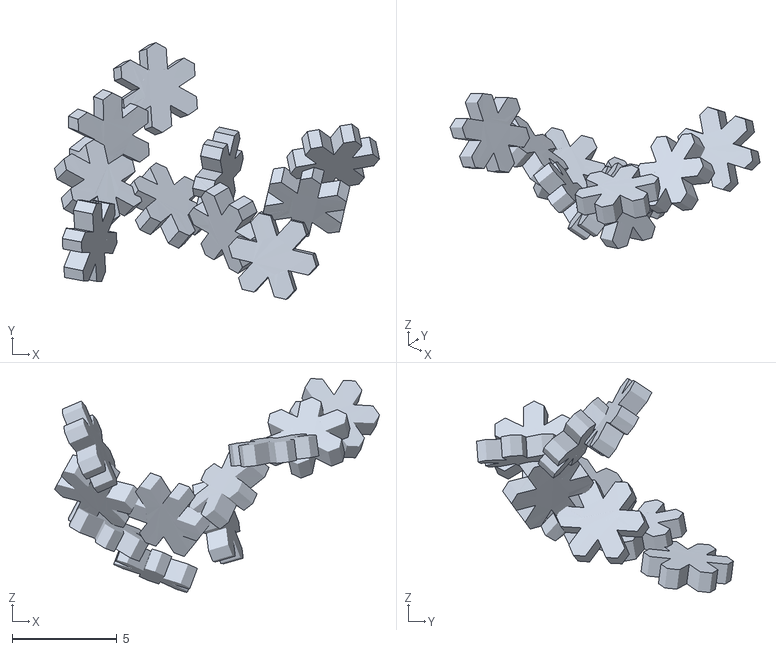
[picture p108: CAD file, 2023-11-13]
Resin Printing/Snowflakes/3D_Files/Ag,1,St100.stl
15.5 x 12.3 x 10.2
