hthant/snowteam_2023_2024/Resin Printing/Snowflakes/3D_Files/D1,20,0.04.stl

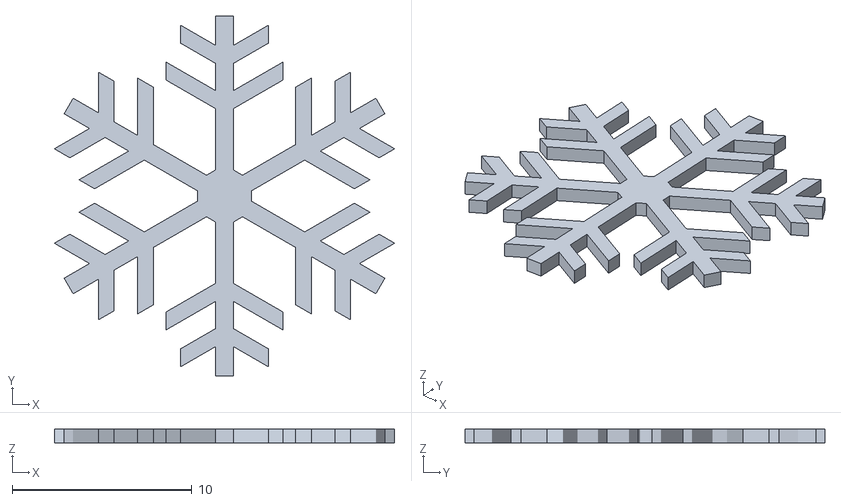
[picture p109: CAD file, 2023-11-13]
Resin Printing/Snowflakes/3D_Files/D1,20,0.04.stl
18.9 x 20.0 x 0.8
