hthant/snowteam_2023_2024/Resin Printing/Snowflakes/3D_Files/CR,5,5,12.stl

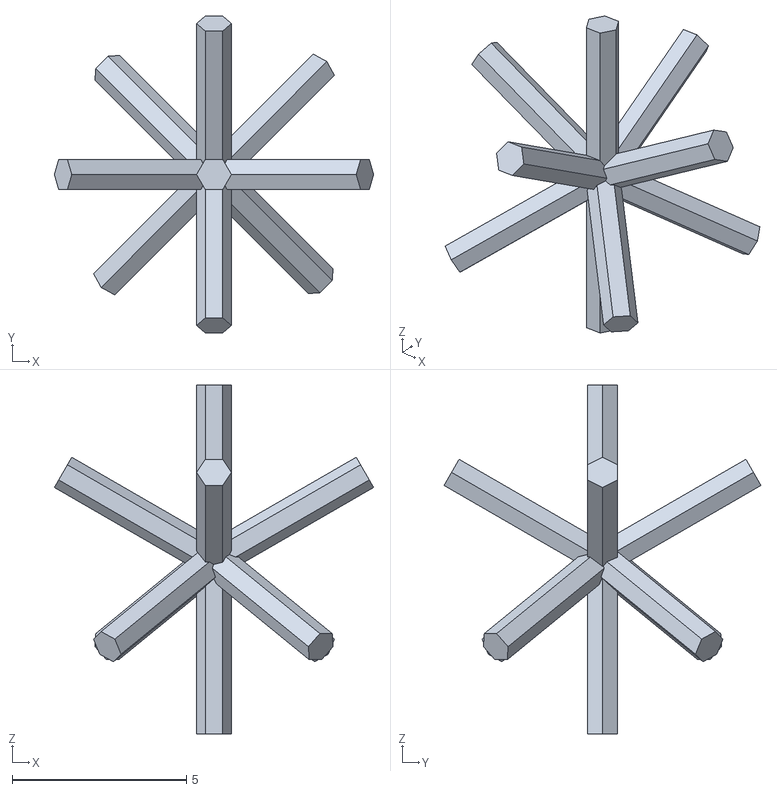
[picture p110: CAD file, 2023-11-13]
Resin Printing/Snowflakes/3D_Files/CR,5,5,12.stl
9.16 x 9.09 x 10.0
