hthant/snowteam_2023_2024/Resin Printing/Snowflakes/3D_Files/CR,7,5,12.stl

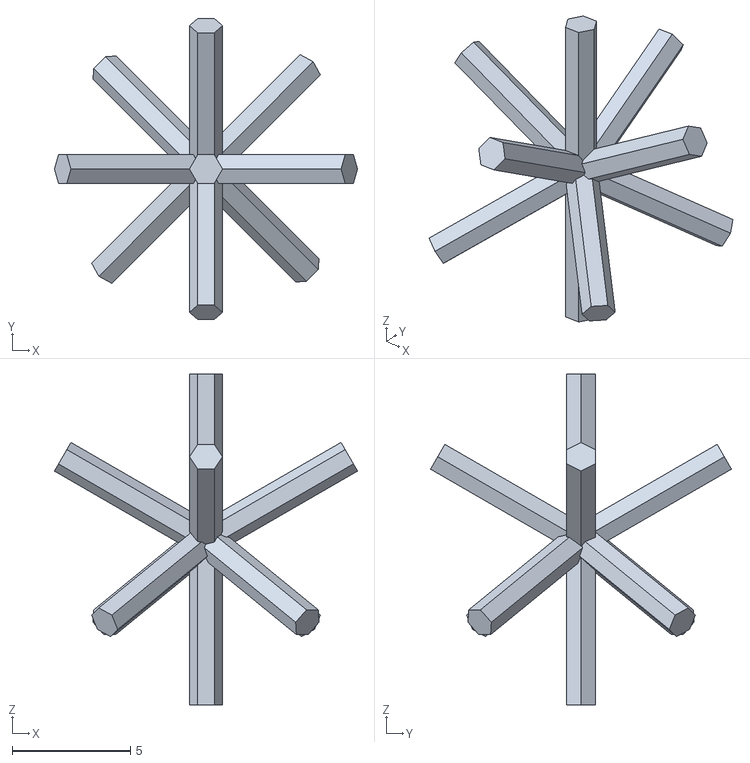
[picture p111: CAD file, 2023-11-13]
Resin Printing/Snowflakes/3D_Files/CR,7,5,12.stl
12.8 x 12.7 x 14.0
