hthant/snowteam_2023_2024/Resin Printing/Snowflakes/3D_Files/CC,15,2,Hex.stl

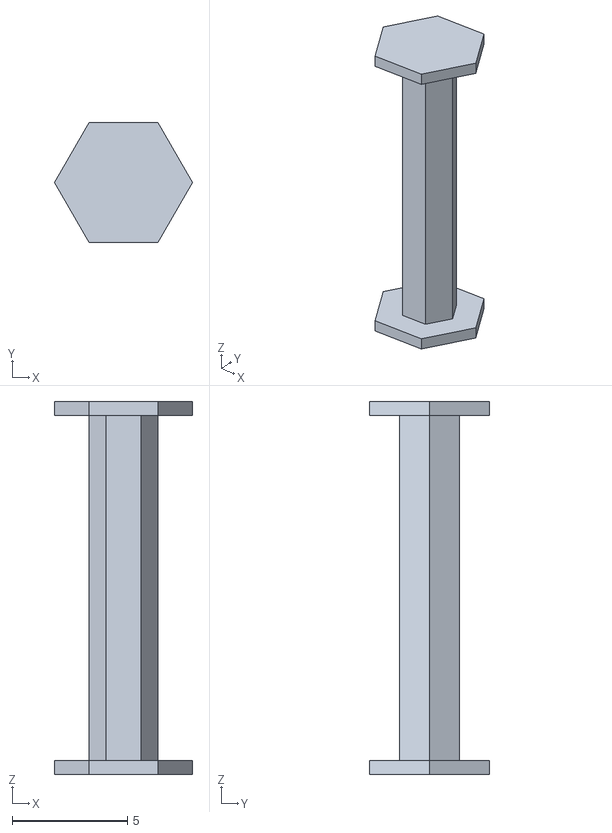
[picture p112: CAD file, 2023-11-13]
Resin Printing/Snowflakes/3D_Files/CC,15,2,Hex.stl
6.00 x 5.20 x 16.2
