hthant/snowteam_2023_2024/Resin Printing/Snowflakes/3D_Files/D1,15,0.04.stl

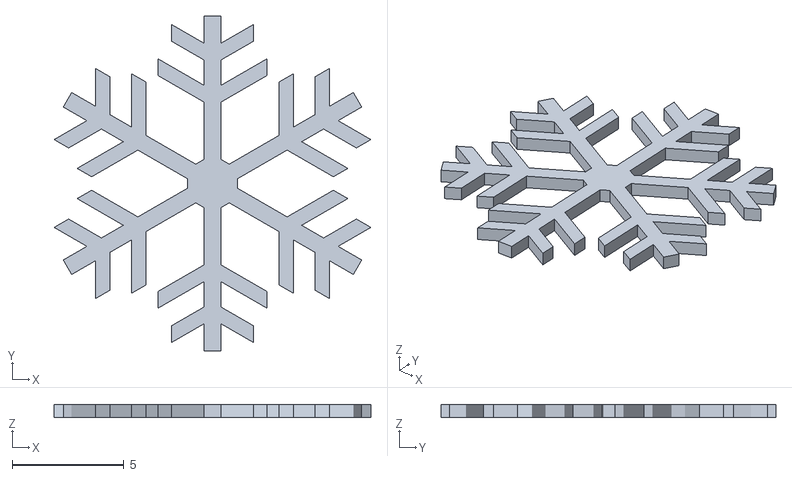
[picture p113: CAD file, 2023-11-13]
Resin Printing/Snowflakes/3D_Files/D1,15,0.04.stl
14.2 x 15.0 x 0.6
