hthant/snowteam_2023_2024/Resin Printing/Snowflakes/3D_Files/CC,20,2,Hex.stl

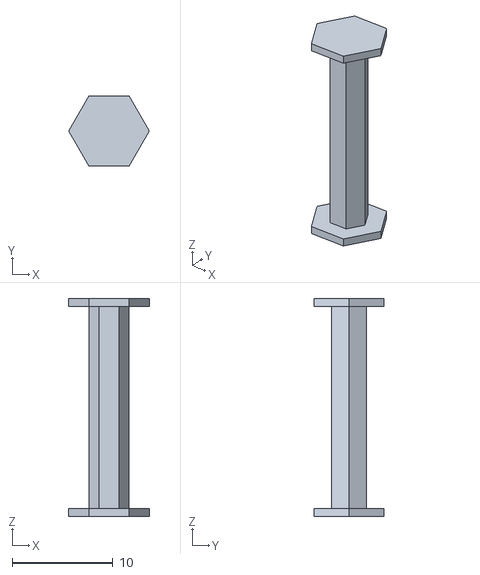
[picture p114: CAD file, 2023-11-13]
Resin Printing/Snowflakes/3D_Files/CC,20,2,Hex.stl
8.00 x 6.93 x 21.6
