hthant/snowteam_2023_2024/solidworks_senior_design/assemblybaseandtop.SLDASM

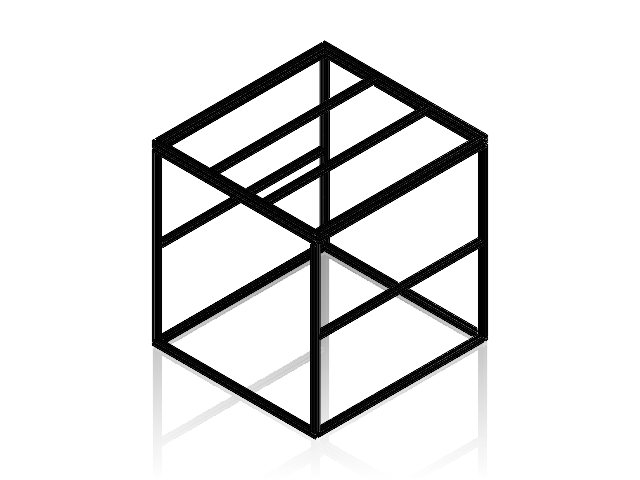
[picture p117: CAD file, 2023-11-08]
solidworks_senior_design/assemblybaseandtop.SLDASM
MakerBeam Profile 10x10x350.step x 20
