hthant/snowteam_2023_2024/solidworks_senior_design/8020_1.0inchbaseandtop.SLDASM

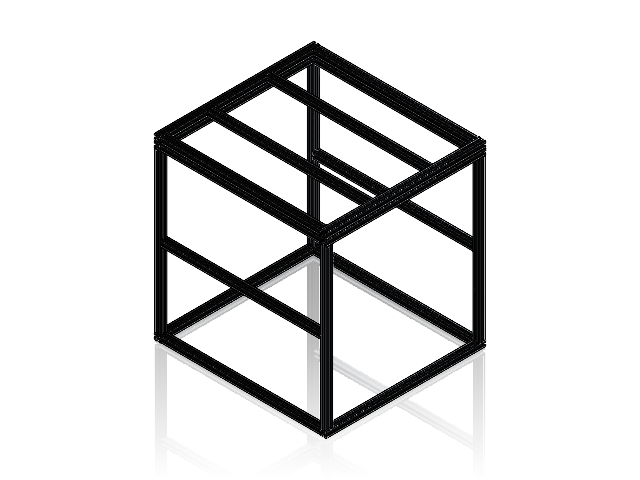
[picture p118: CAD file, 2023-11-08]
solidworks_senior_design/8020_1.0inchbaseandtop.SLDASM
8020_1.0inchbeam x 20
