hthant/snowteam_2023_2024/Light Fixtures/Heatsink/heatsinkdimensions.pdf

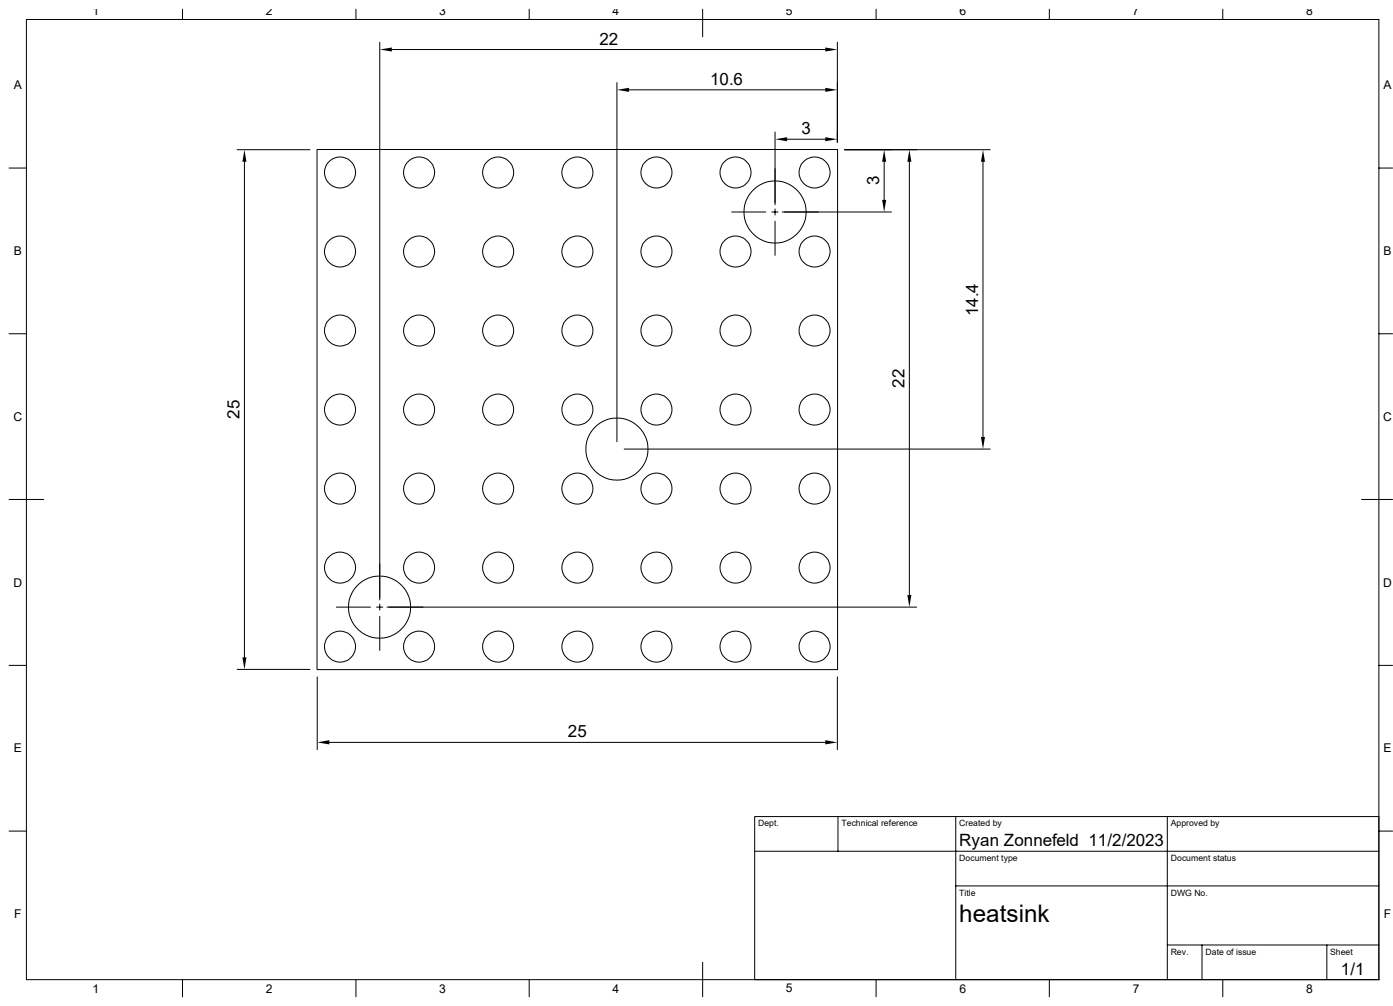
[picture p121: page 1]
Dept.; Technical reference; Created by; Approved by; Document type; Document status Title; DWG No. Rev.; Date of issue; Sheet 11/2/2023; heatsink; Ryan Zonnefeld
