hthant/snowteam_2023_2024/SMAS trigger board/camera_trigger.kicad_sch

## KiCad design SMAS trigger board/camera_trigger.kicad_sch (2023-11-14)

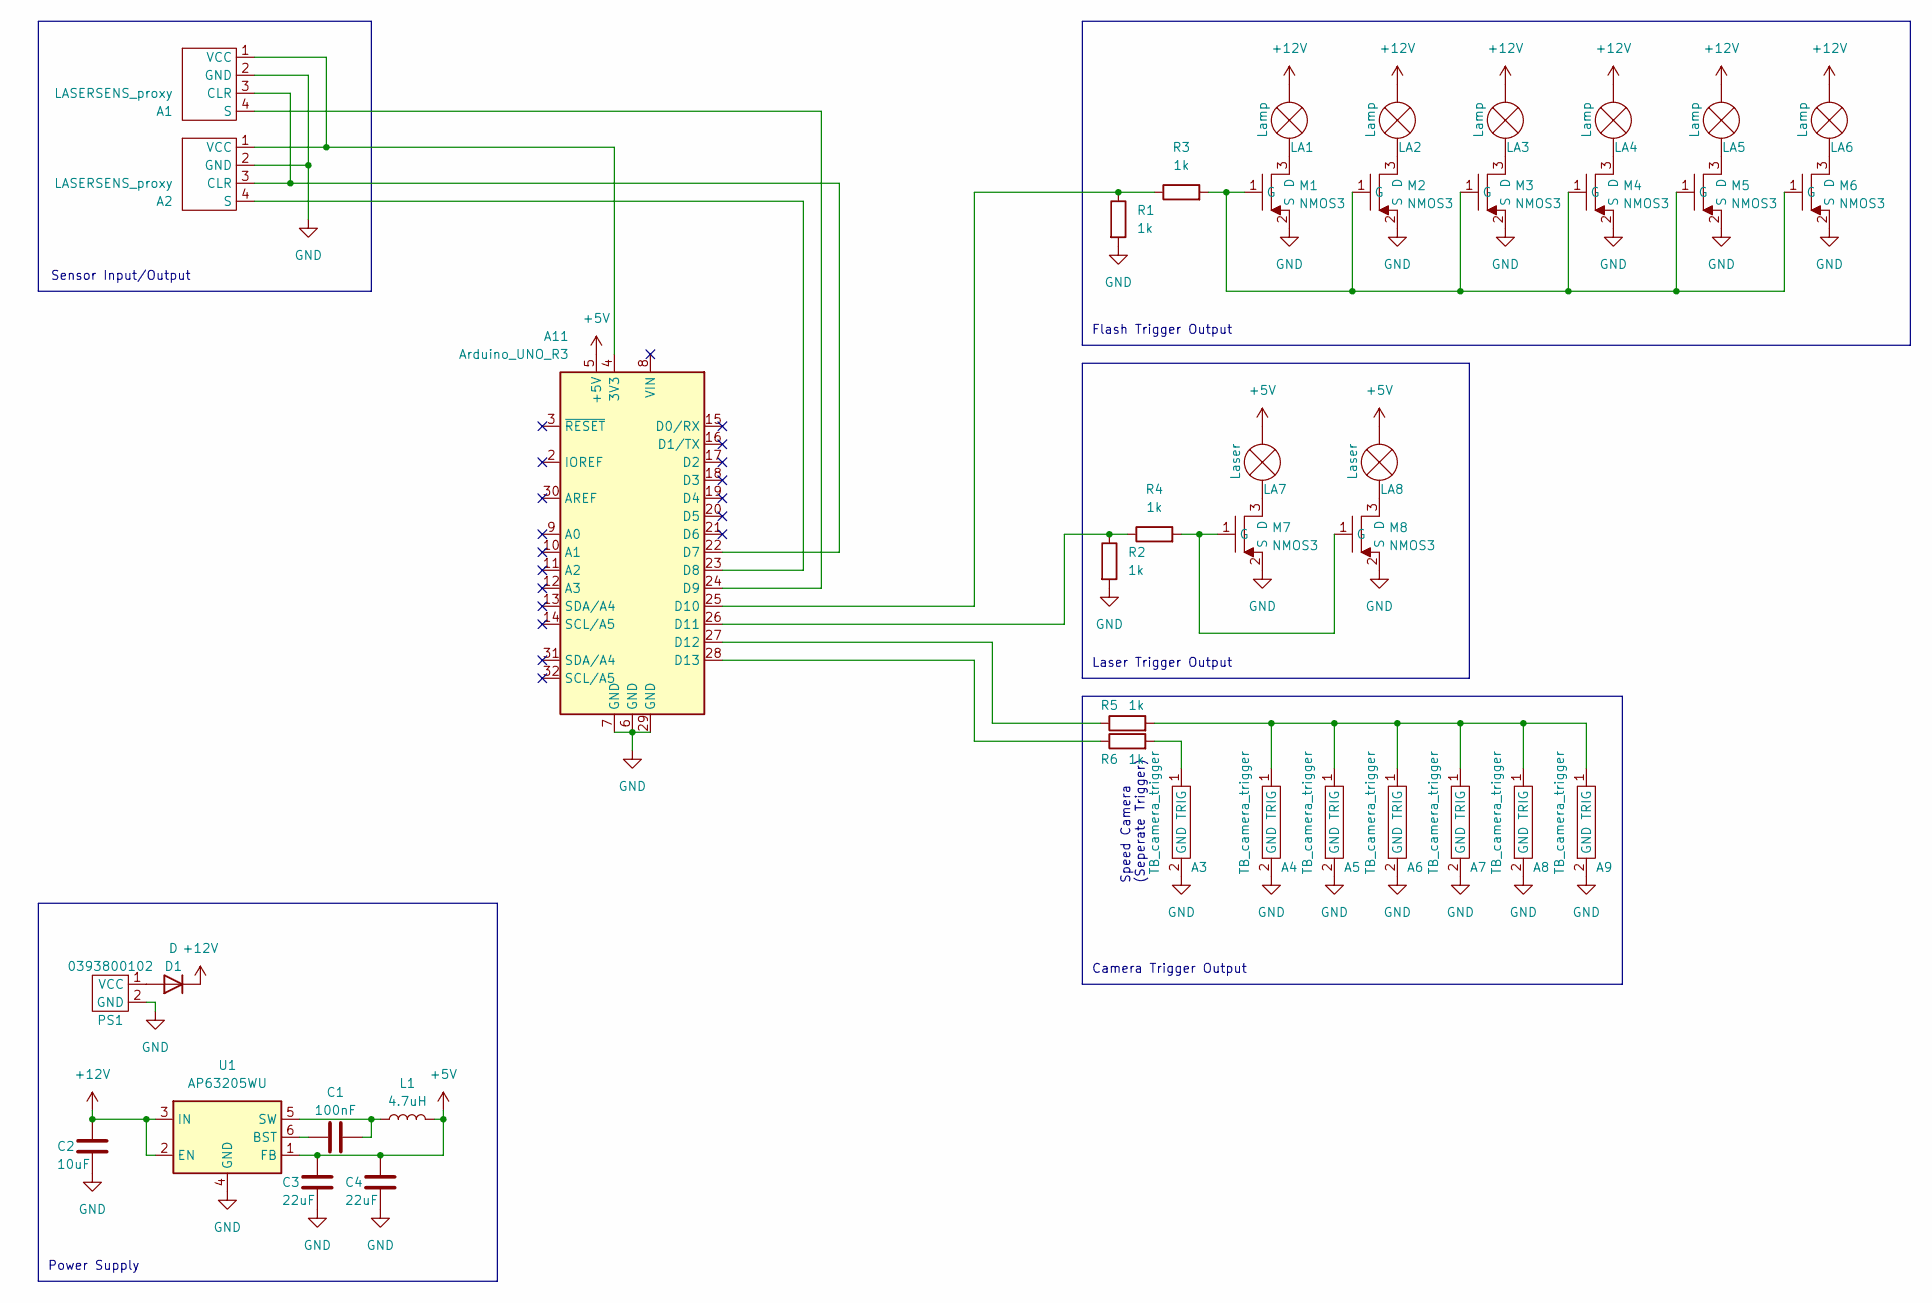
[picture p122: schematic camera_trigger.kicad_sch]

Parts:
A1, A2: LASERSENS_proxy; JST-XH_4pin
A3, A4, A5, A6, A7, A8, A9: TB_camera_trigger; JST-XH_2pin
A11: Arduino_UNO_R3
C1: 100nF; C_01005_0402Metric_Pad0.57x0.30mm_HandSolder
C2: 10uF; C_0805_2012Metric_Pad1.18x1.45mm_HandSolder
C3, C4: 22uF; C_0603_1608Metric_Pad1.08x0.95mm_HandSolder
D1: D; TO-277B
L1: 4.7uH; L_1008_2520Metric_Pad1.43x2.20mm_HandSolder
LA1, LA2, LA3, LA4, LA5, LA6: Lamp; JST-XH_2pin
LA7, LA8: Laser; JST-XH_2pin
M1, M2, M3, M4, M5, M6, M7, M8: NMOS3; SOT-23
PS1: 0393800102; MOLEX_0393800102
R1, R2, R3, R4, R5, R6: 1k; R_1206_3216Metric_Pad1.30x1.75mm_HandSolder
U1: AP63205WU; TSOT-23-6

Connections:
+5V: A11.5 (+5V), C3.2, C4.2, L1.2, LA7.2 (+), LA8.2 (+), U1.1 (FB)
+12V: C2.2, D1.2 (K), LA1.2 (+), LA2.2 (+), LA3.2 (+), LA4.2 (+), LA5.2 (+), LA6.2 (+), U1.2 (EN), U1.3 (IN)
GND: A1.2 (GND), A2.2 (GND), A3.2 (GND), A4.2 (GND), A5.2 (GND), A6.2 (GND), A7.2 (GND), A8.2 (GND), A9.2 (GND), A11.6 (GND), A11.7 (GND), A11.29 (GND), C2.1, C3.1, C4.1, M1.2 (S), M2.2 (S), M3.2 (S), M4.2 (S), M5.2 (S), M6.2 (S), M7.2 (S), M8.2 (S), PS1.2 (GND), R1.2, R2.2, U1.4 (GND)
unnamed: A1.1 (VCC), A2.1 (VCC), A11.4 (3V3)
unnamed: A1.3 (CLR), A2.3 (CLR), A11.22 (D7)
unnamed: A1.4 (S), A11.24 (D9)
unnamed: A3.1 (TRIG), R6.2
unnamed: A4.1 (TRIG), A5.1 (TRIG), A6.1 (TRIG), A7.1 (TRIG), A8.1 (TRIG), A9.1 (TRIG), R5.2
unnamed: A2.4 (S), A11.23 (D8)
unnamed: A11.25 (D10), R1.1, R3.1
unnamed: A11.26 (D11), R2.1, R4.1
unnamed: A11.27 (D12), R5.1
unnamed: A11.28 (D13), R6.1
unnamed: C1.1, U1.6 (BST)
unnamed: C1.2, L1.1, U1.5 (SW)
unnamed: D1.1 (A), PS1.1 (VCC)
unnamed: LA1.1 (-), M1.3 (D)
unnamed: LA2.1 (-), M2.3 (D)
unnamed: LA3.1 (-), M3.3 (D)
unnamed: LA4.1 (-), M4.3 (D)
unnamed: LA5.1 (-), M5.3 (D)
unnamed: LA6.1 (-), M6.3 (D)
unnamed: LA7.1 (-), M7.3 (D)
unnamed: LA8.1 (-), M8.3 (D)
unnamed: M1.1 (G), M2.1 (G), M3.1 (G), M4.1 (G), M5.1 (G), M6.1 (G), R3.2
unnamed: M7.1 (G), M8.1 (G), R4.2

Notes on the sheet:
Flash Trigger Output
Sensor Input/Output
Laser Trigger Output
Power Supply
Camera Trigger Output
Speed Camera (Seperate Trigger)
