hthant/snowteam_2023_2024/MASC photos/71504698309--9B7097F0-AAFB-41AE-ACB9-E4E6F074DC68.jpg

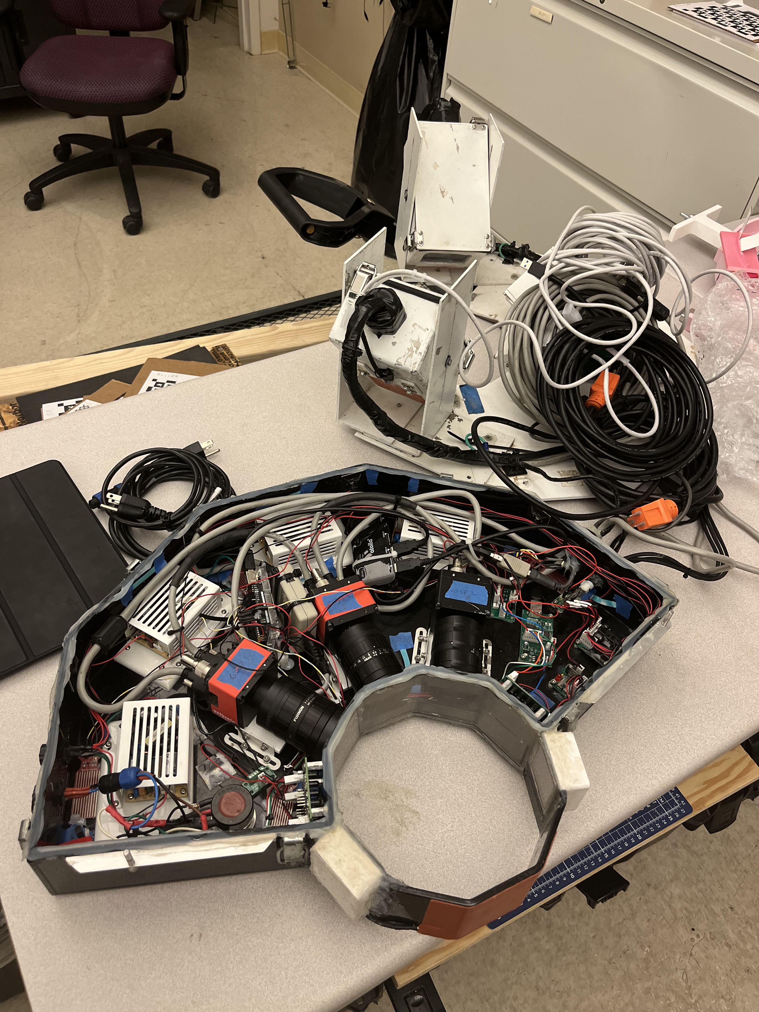
MASC photos/71504698309--9B7097F0-AAFB-41AE-ACB9-E4E6F074DC68.jpg
