hthant/snowteam_2023_2024/MASC photos/IMG-0115.jpg

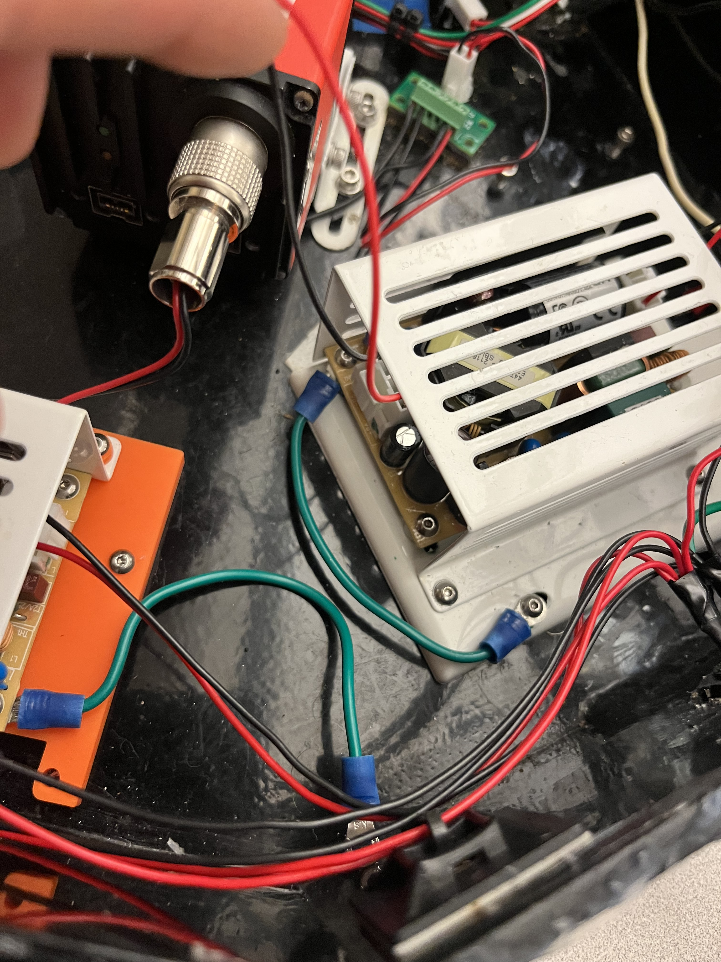
MASC photos/IMG-0115.jpg
