hthant/snowteam_2023_2024/MASC photos/IMG-0382.jpg

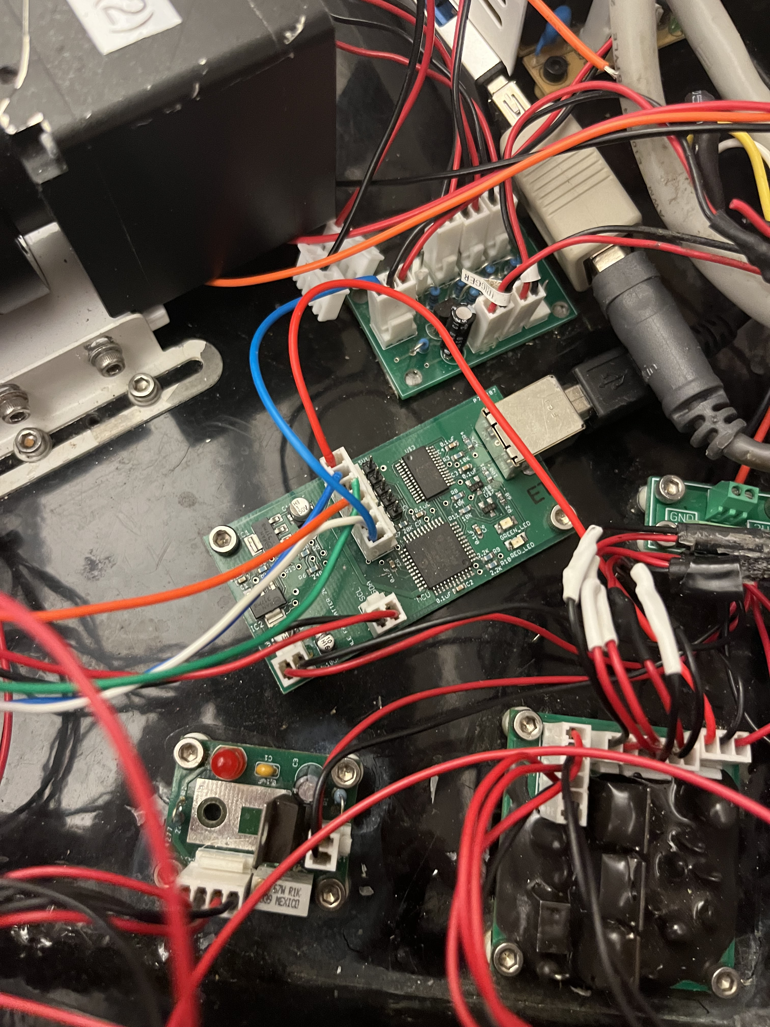
MASC photos/IMG-0382.jpg
