hthant/snowteam_2023_2024/MASC photos/IMG-8710.jpg

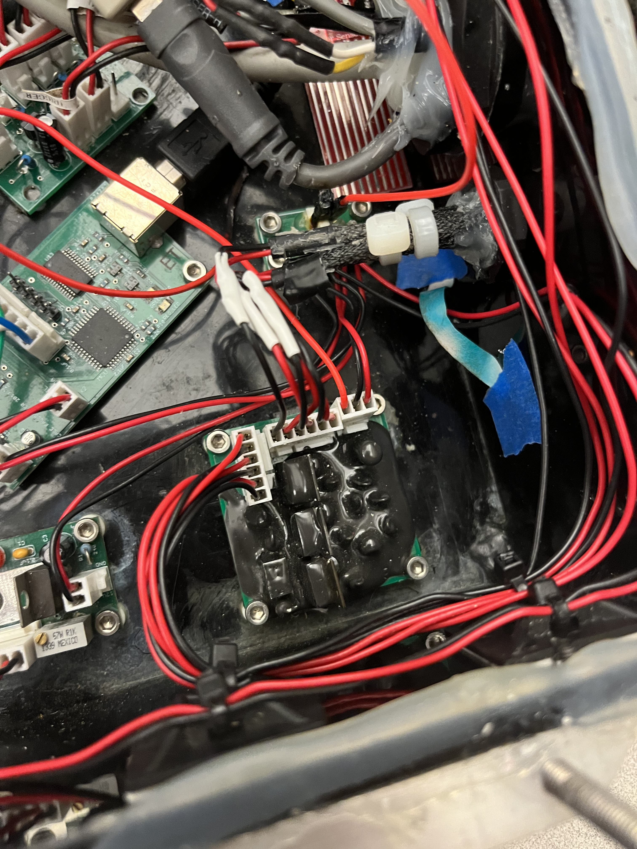
MASC photos/IMG-8710.jpg
